palette-system/az-macro/docs/az66jp/rgbled/README.md

# RGBLEDの設定方法
<br>

<table>
  <tr>
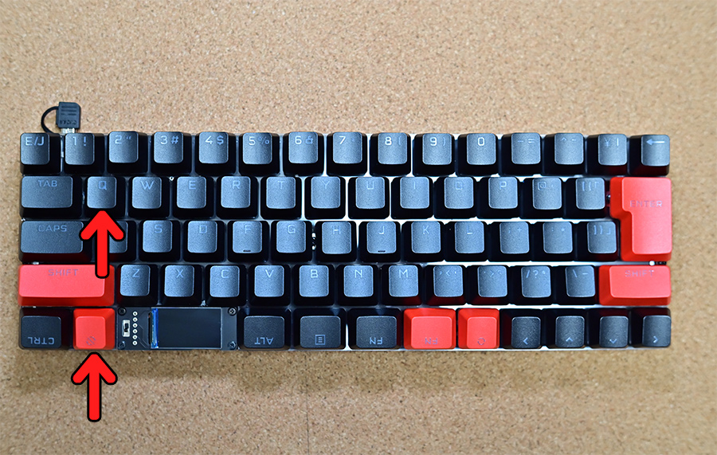
[picture p16: images/az66jp/led_setting_5.jpg]
    <td><br>
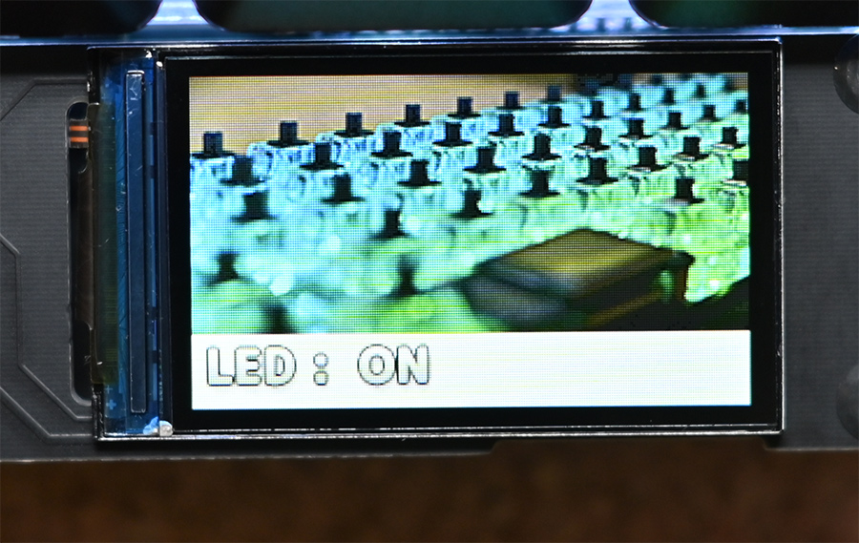
[picture p17: images/az66jp/led_setting_1.jpg]
    </td>
    <td valign="top">
    <b>キー：</b> Fn ＋ Q<br><br>
    <b>ON / OFF</b><br>
    カラーLEDの ON / OFF が切り替えできます。
  </tr>
  <tr>
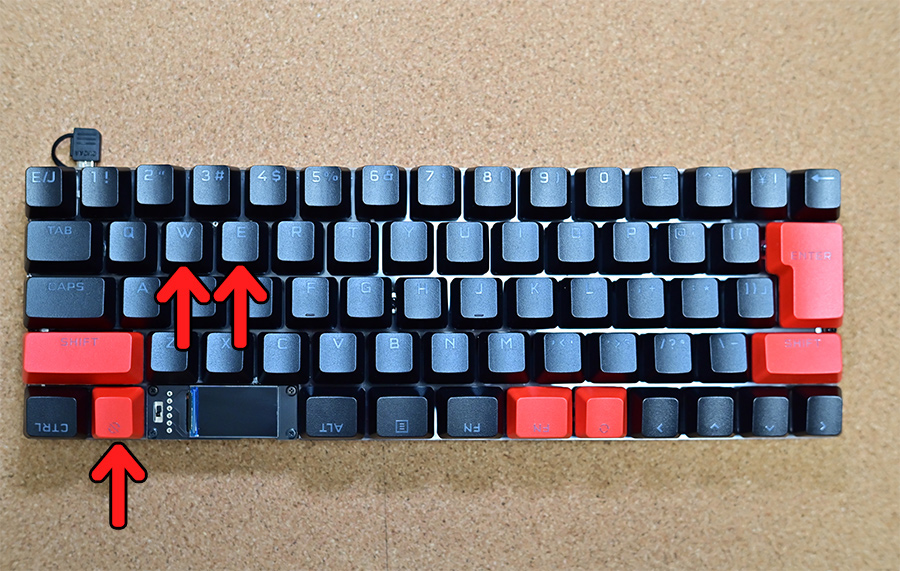
[picture p18: images/az66jp/led_setting_6.jpg]
    <td><br>
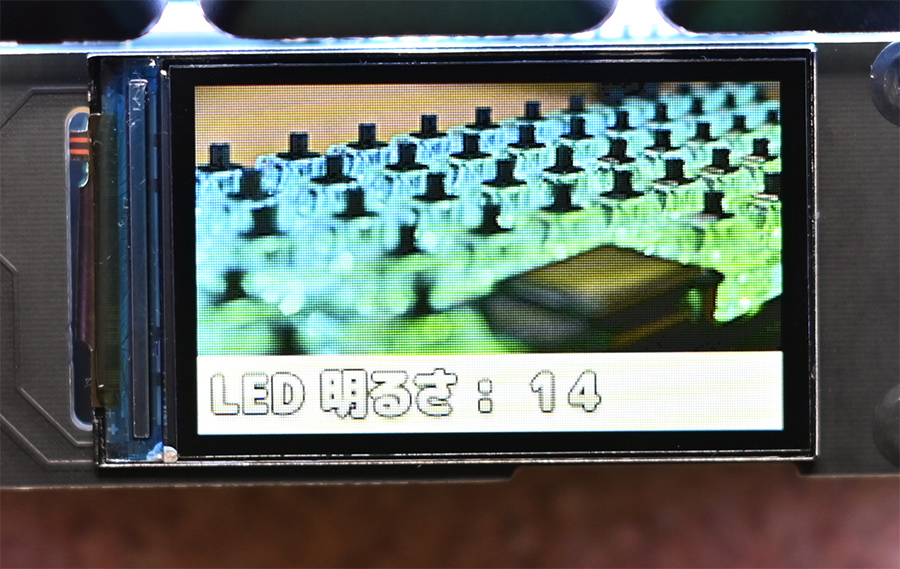
[picture p19: images/az66jp/led_setting_2.jpg]
    </td>
    <td valign="top">
    <b>明るさUP：</b> Fn ＋ W<br><br>
    <b>明るさDOWN：</b> Fn ＋ E<br><br>
    <b>明るさ UP / DOWN</b><br>
    LEDの明るさを0～16段階で設定できます。<br>
  </tr>
  <tr>
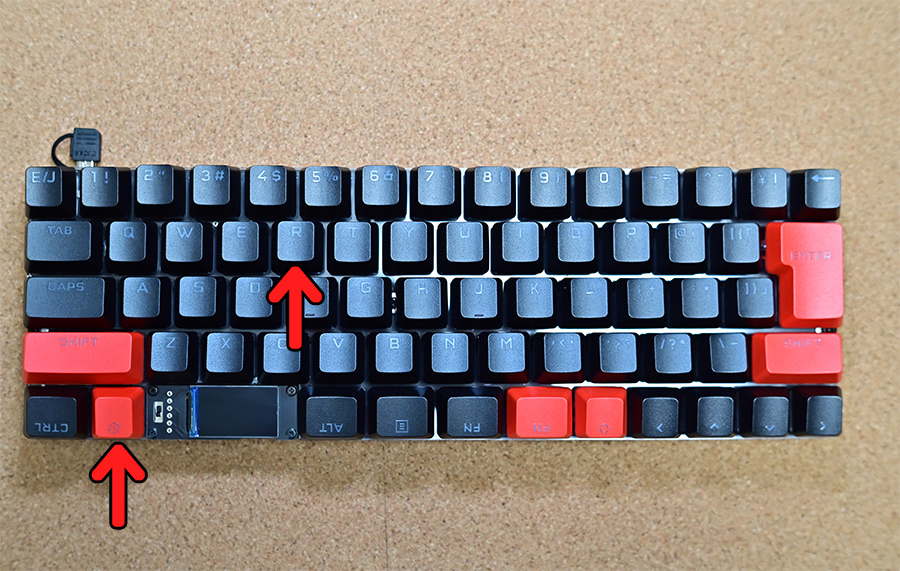
[picture p20: images/az66jp/led_setting_8.jpg]
    <td><br>
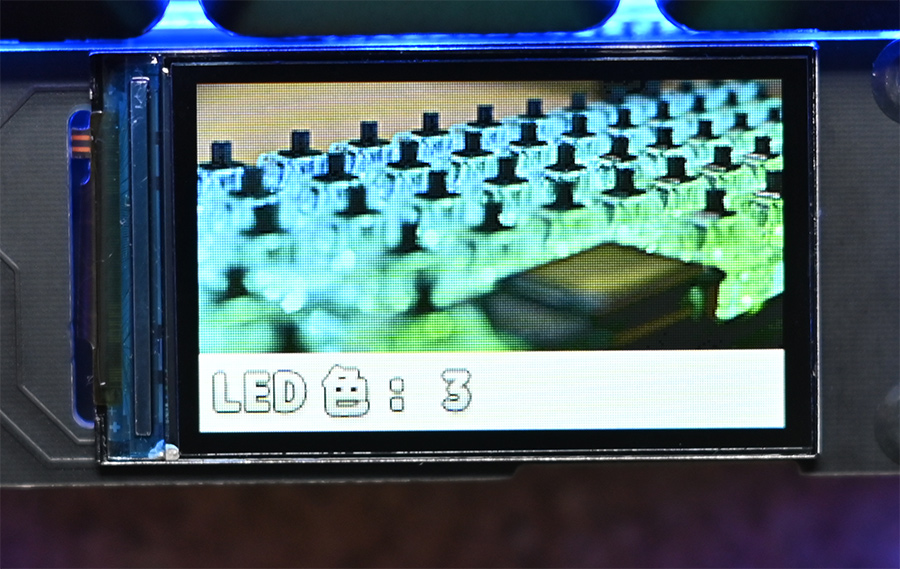
[picture p21: images/az66jp/led_setting_3.jpg]
    </td>
    <td valign="top">
    <b>キー：</b> Fn ＋ R<br><br>
    <b>色変更</b><br>
    光らせるLEDの色を0～5段階で変更できます。<br><br>
    　<b>0 : </b> 白<br>
    　<b>1 : </b> 赤<br>
    　<b>2 : </b> 緑<br>
    　<b>3 : </b> 青<br>
    　<b>4 : </b> 黄<br>
    　<b>5 : </b> 水色<br>
    </td>
  </tr>
  <tr>
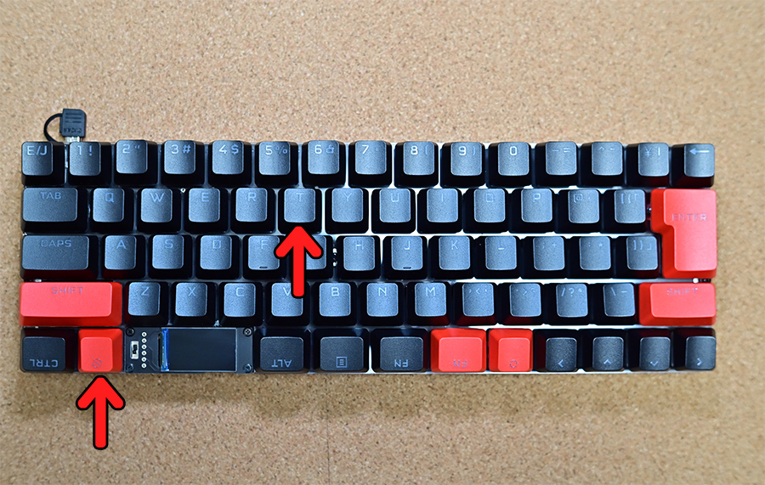
[picture p22: images/az66jp/led_setting_9.jpg]
    <td><br>
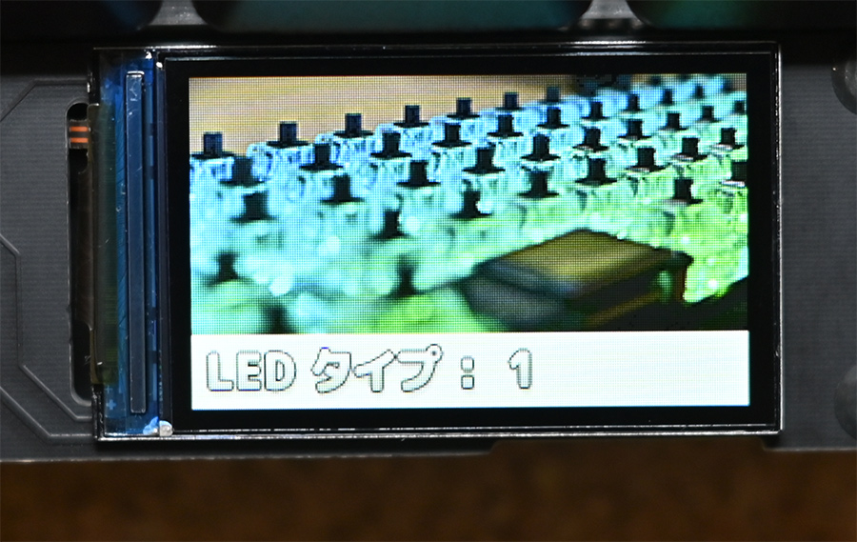
[picture p23: images/az66jp/led_setting_4.jpg]
    </td>
    <td valign="top">
    <b>キー：</b> Fn ＋ T<br><br>
    <b>光らせ方変更</b><br>
    光り方を0～3の4タイプ変更できます。<br><br>
    　<b>0 : </b> 常に点灯<br>
    　<b>1 : </b> 打鍵キーだけ点灯<br>
    　<b>2 : </b> 打鍵キーから周りに広がっていく<br>
    　<b>3 : </b> 常に全てのキーをグラデーション点灯<br>
    </td>
  </tr>
</table>

<br>
<br>
