palette-system/az-macro/docs/az66jp/keydata/README.md

# キー情報

## キーID

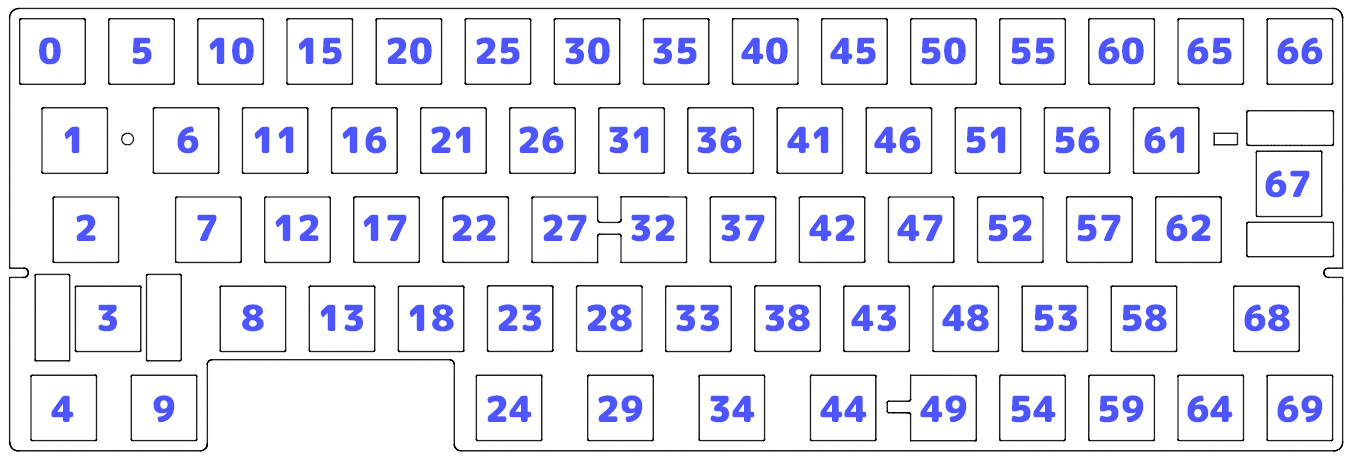
[picture p29: images/az66jp/az66jp_key_id.jpg]


<br>

## LED ID

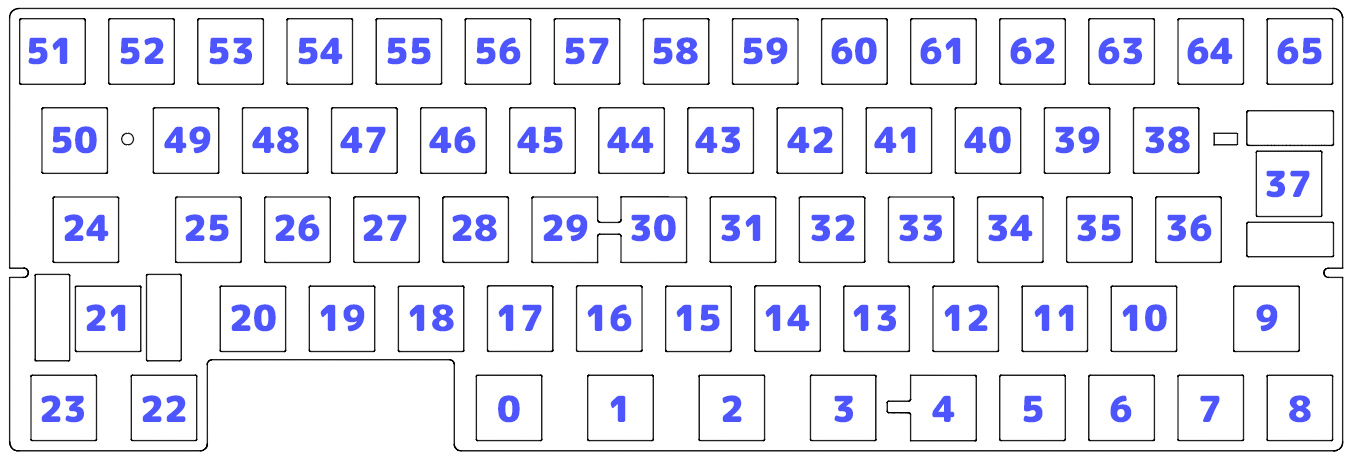
[picture p30: images/az66jp/az66jp_led_num.jpg]
