palette-system/az-macro/docs/setting/key/led/README.md

# キー設定 ＞ LED設定ボタン

<table>
  <tr>
  <td valign="top">
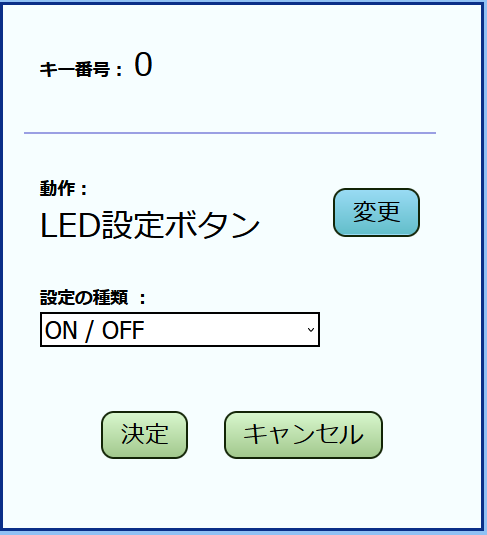
[picture p31: images/key_setting_led.png]
    
    </td>
  <td valign="top">
    <b>設定の種類：ON / OFF</b><br>LEDを光らせるかどうかを変更できます。<br><br>
    <b>設定の種類：明るさUP</b><br>LEDの光の強さを強くします。(0 - 16)<br><br>
    <b>設定の種類：明るさDOWN</b><br>LEDの光の強さを弱くします。(0 - 16)<br><br>
    <b>設定の種類：色変更</b><br>光らせるベースの色を変更できます。(0 - 5)<br><br>
    <b>設定の種類：光らせ方変更</b><br>LEDの光り方を変更できます。(0 -4)<br>
    <br>
    <b>決定：</b><br>　変更した内容を反映してトップに戻ります。<br>
    <br>
    <b>キャンセル：</b><br>　変更した内容を反映せずに設定トップに戻ります。<br>
  </td>
  </tr>
</table>
