palette-system/az-macro/docs/az66jp/heatmap/README.md

# 打鍵ヒートマップ機能の使い方
<br>

<table>
  <tr>
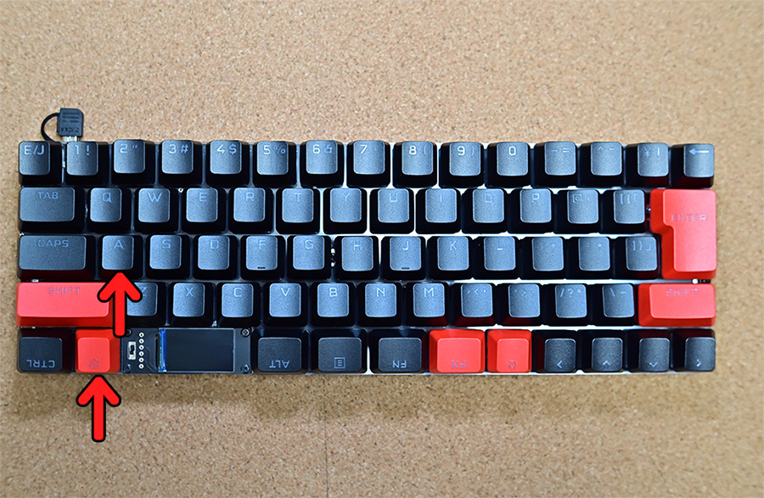
[picture p58: images/az66jp/dakey_1.jpg]
    <td><br>
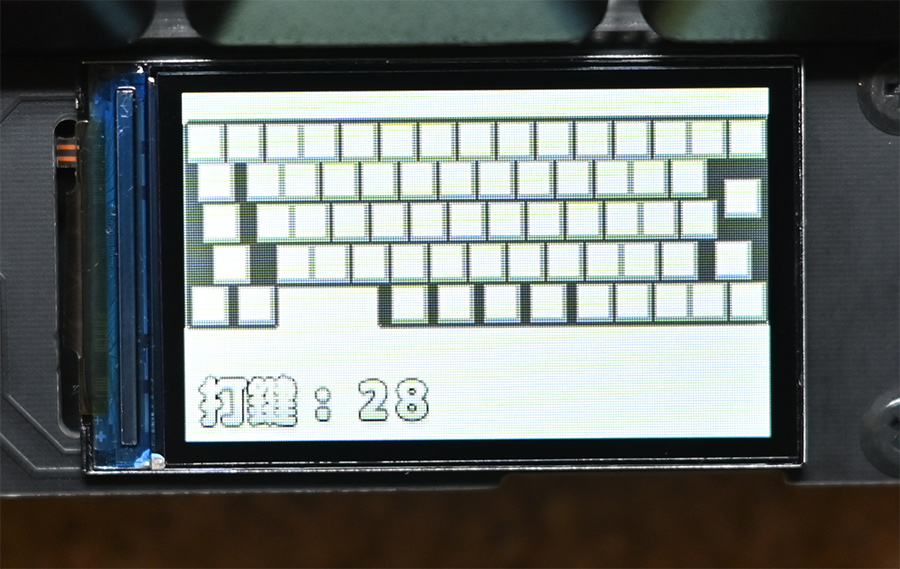
[picture p59: images/az66jp/dakey_6.jpg]
    </td>
    <td valign="top">
    <b>キー：</b> Fn ＋ A<br><br>
    <b>ヒートマップ表示</b><br>
    液晶プレートに打鍵ヒートマップを表示します。<br>
    もう一度押すと元の待ち受け表示に戻ります。</td>
  </tr>
  <tr>
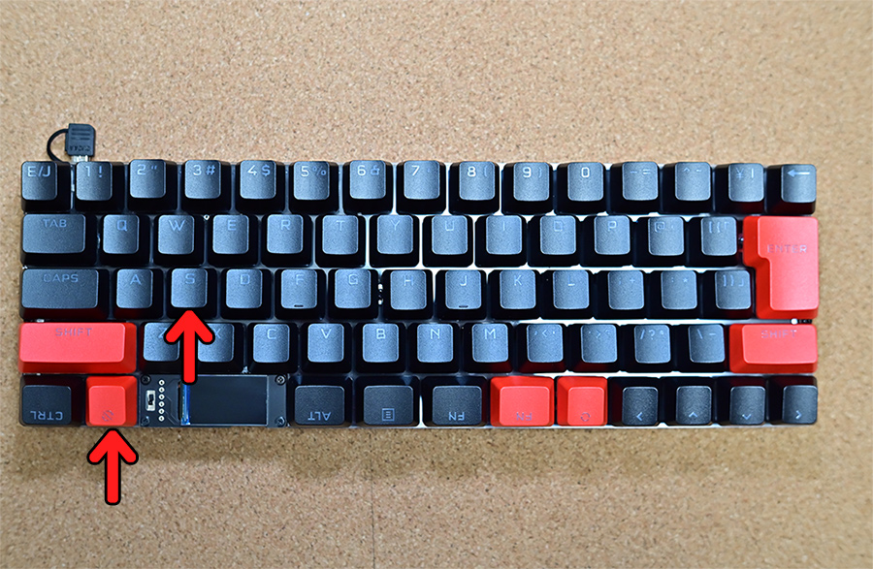
[picture p60: images/az66jp/dakey_2.jpg]
    <td><br>
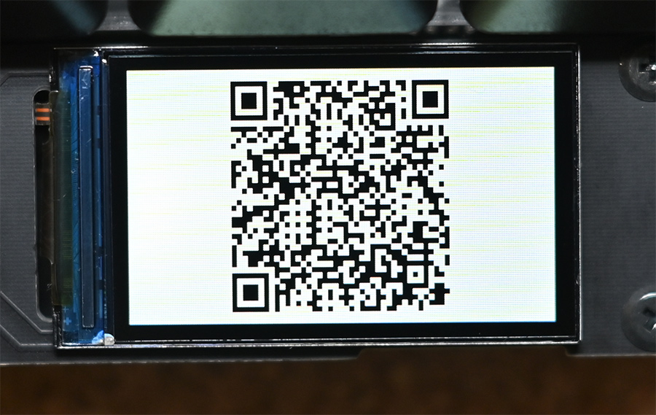
[picture p61: images/az66jp/dakey_5.jpg]
    </td>
    <td valign="top">
    <b>キー：</b> Fn ＋ S<br><br>
    <b>QRコード</b><br>
    現在の打鍵情報をazkey.jpに送信して、スマホやPCから打鍵数を見れるURLのQRコードを表示します。<br>
    何かキーを押すとQRコードの表示が終わります。<br><br>
    ※ 設定ページでWifi接続の設定がしてある必要があります。</td>
  </tr>
  <tr>
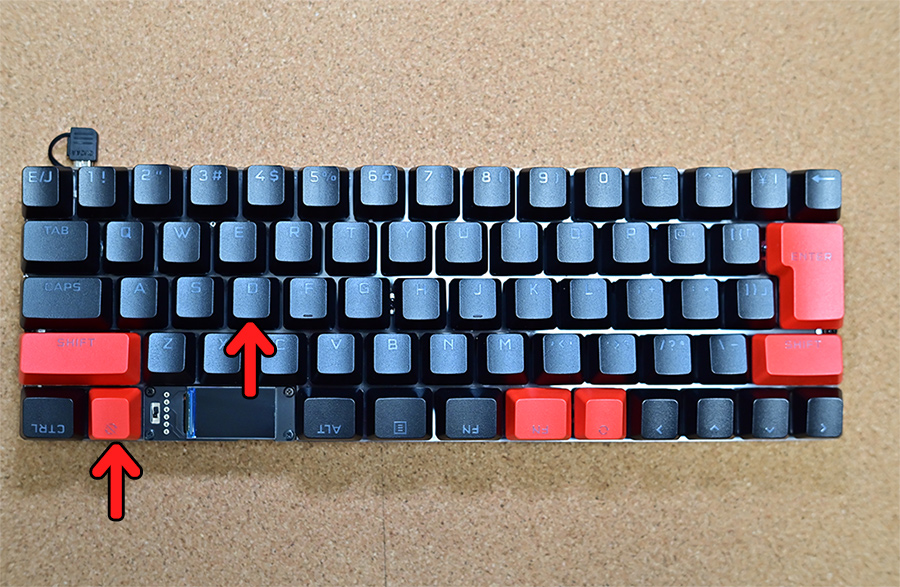
[picture p62: images/az66jp/dakey_3.jpg]
    <td><br>
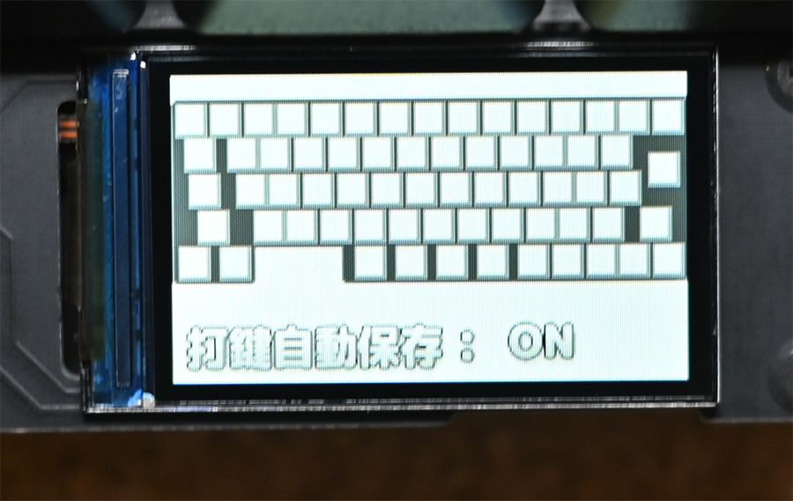
[picture p63: images/az66jp/dakey_7.jpg]
    </td>
    <td valign="top">
    <b>キー：</b> Fn ＋ D<br><br>
    <b>自動保存設定</b><br>
    30分おきに打鍵数を保存するかどうかを変更できます。<br>
    通常は「打鍵数保存」キーを押したタイミングでのみデータを保持していきますが、自動保存設定をONにすると30分おきの情報も保存されます。<br>
    細かくデータが残っていると、QRコードを読み込んでPCやスマホで見た時の時間グラフが細かく表示されます。<br><br>
    ※ 設定ページでWifi接続の設定がしてある必要があります。</td>
  </tr>
  <tr>
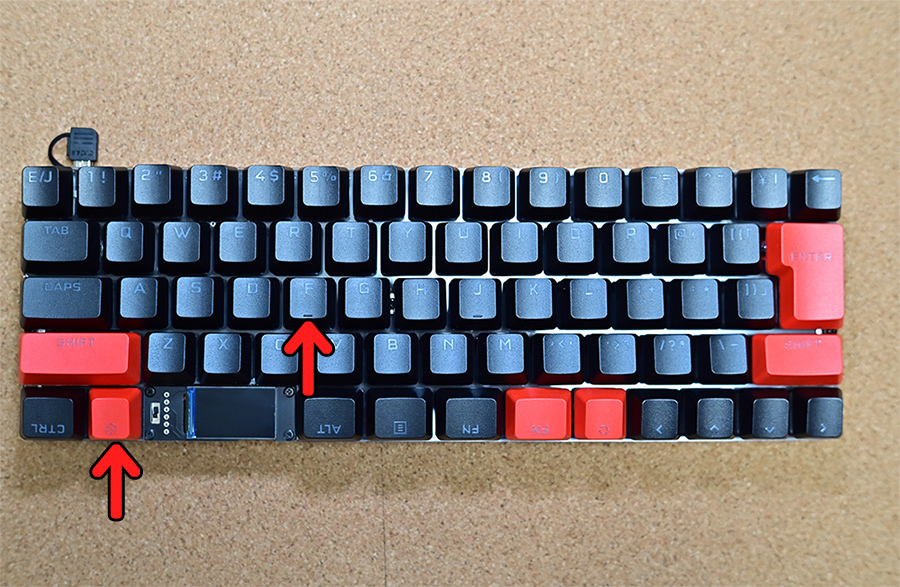
[picture p64: images/az66jp/dakey_4.jpg]
    <td><br>
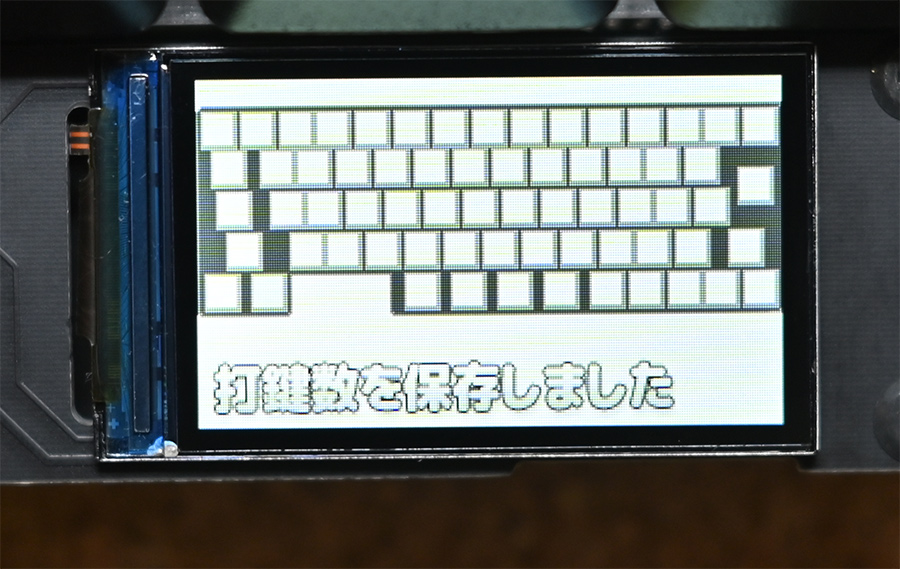
[picture p65: images/az66jp/dakey_8.jpg]
    </td>
    <td valign="top">
    <b>キー：</b> Fn ＋ F<br><br>
    <b>打鍵数保存</b><br>
    現在の打鍵数を保存します。<br>
    細かくデータが残っていると、QRコードを読み込んでPCやスマホで見た時の時間グラフが細かく表示されます。<br><br>
    ※ 設定ページでWifi接続の設定がしてある必要があります。</td>
  </tr>
</table>

<br>
<br>
