palette-system/az-macro/docs/az66jp/ankey/README.md

# 暗記ボタンの使い方
<br>

<table>
  <tr>
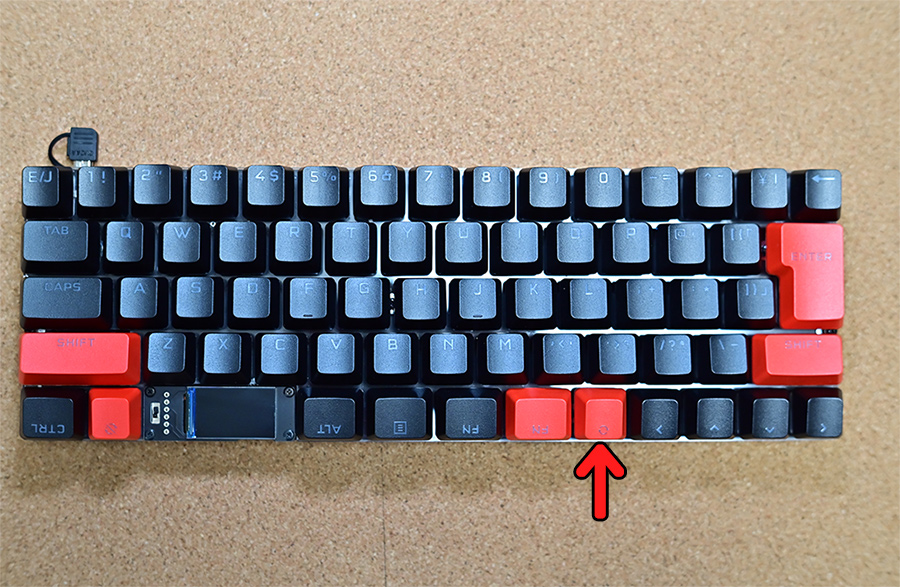
[picture p66: images/az66jp/ankey_1.jpg]
    <td></td>
    <td>暗記ボタンとして登録されているキーを長押しします。</td>
  </tr>
  <tr>
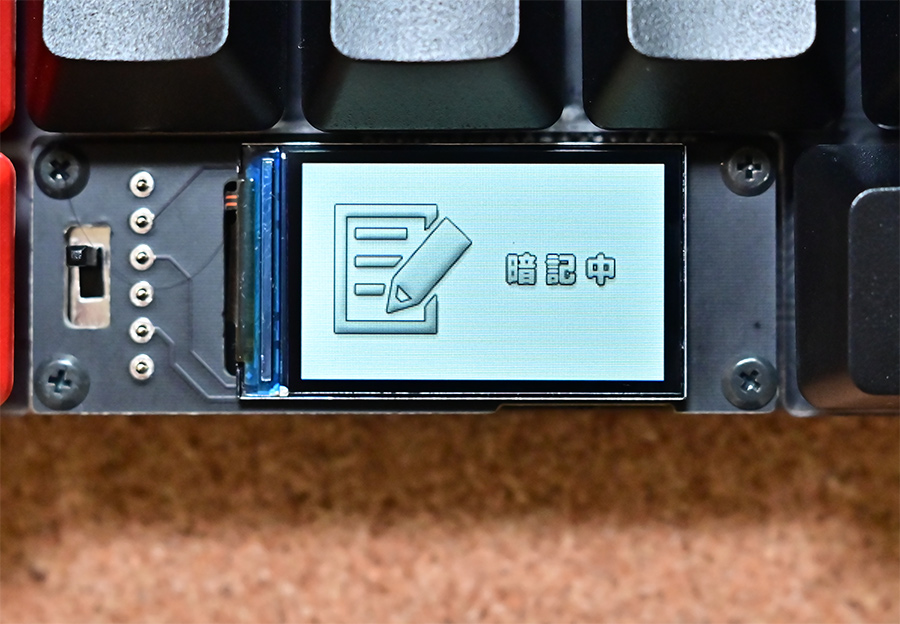
[picture p67: images/az66jp/ankey_2.jpg]
    <td></td>
    <td>液晶プレートに「暗記中」と表示されたら暗記モードに入りましたので、暗記ボタンを離してください。</td>
  </tr>
  <tr>
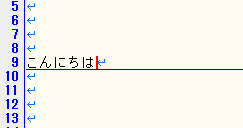
[picture p68: images/az66jp/ankey_3.jpg]
    <td></td>
    <td>暗記モード中にAZ-66JPでキー入力した内容が全て暗記されます。<br><br>
    ※ キーの「押した」「離した」のデータがAZ-66JP内に保存されます。<br>
    ※ １ボタンに対して最大で1000入力まで記憶でき、最大値に達した時点で暗記モードが終了します。<br>
    ※ ここで暗記したデータは電源を落としても残ります。<br><br>
    暗記モードに入る時に長押しした暗記ボタンを短押しすると暗記モード終了になります。
    </td>
  </tr>
  <tr>
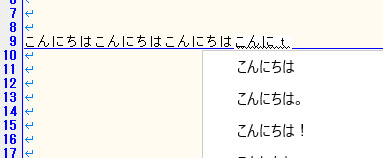
[picture p69: images/az66jp/ankey_4.jpg]
    <td></td>
    <td>暗記データがある状態で暗記ボタンを短押しすると、保存してあるデータが入力されます。<br>
    </td>
  </tr>
</table>

<br>
<br>
