palette-system/az-macro/docs/setting/az66jp/README.md

# AZ-66JP 設定画面の入り方

<table>
  <tr>
  <td valign="top">
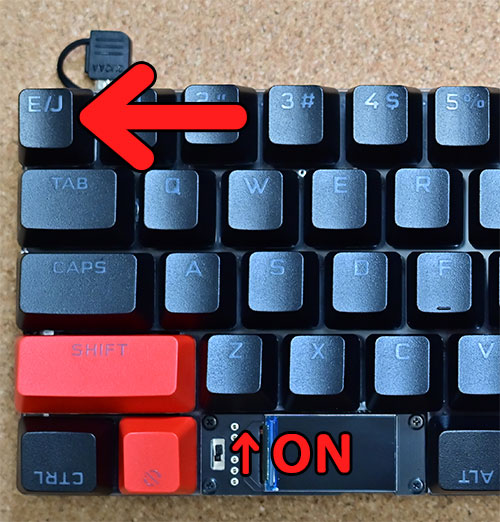
[picture p70: images/az66jp/setting_init.jpg]
    
  </td>
  <td valign="top">
    半角/全角 ボタンを押したままAZ-66JPの電源をONにします。<br>
  </td>
  </tr>
  <tr>
  <td valign="top">
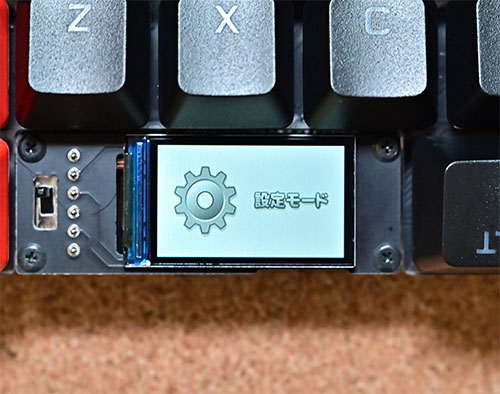
[picture p71: images/az66jp/setting_init_2.jpg]
    
  </td>
  <td valign="top">
    設定モードとして起動すると、液晶プレートに「設定モード」と表示されます。<br><br>
    　※ この画面が出るまで半角/全角ボタンは押したままにして下さい。
  </td>
  </tr>
  <tr>
  <td valign="top">
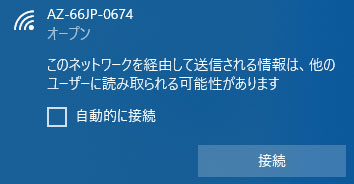
[picture p72: images/az66jp/wifi_ap_setting.jpg]
    
  </td>
  <td valign="top">
    設定モードとして起動した状態で、PCやスマホからWifiアクセスポイントを探すと「AZ-66JP-****」というアクセスポイントがあるので接続します。<br>
  </td>
  </tr>
  <tr>
  <td valign="top">
    
  </td>
  <td valign="top">
    接続完了すると自動的にブラウザが立ち上がり設定画面が開かれます。<br><br>
    　※ 自動的に開かれない場合はブラウザを開き http://192.168.4.1/ にアクセスして下さい。
  </td>
  </tr>
</table>
