palette-system/az-macro/docs/az66jp/photos/README.md

# 商品写真 AZ-66JP

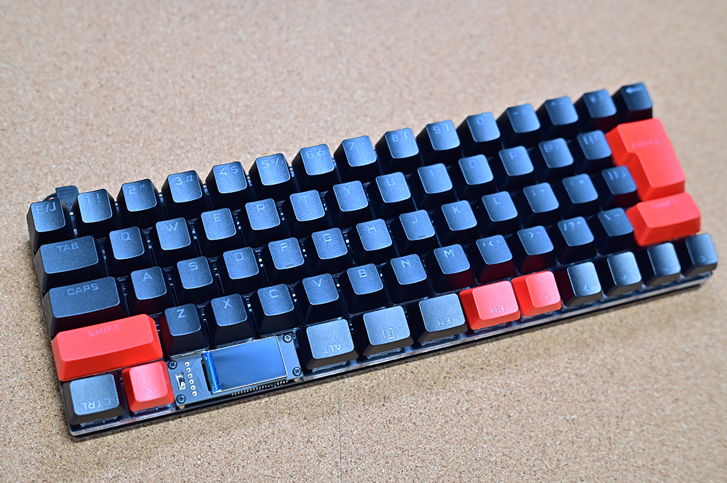
[picture p78: images/az66jp/photo_01.jpg]


<br>

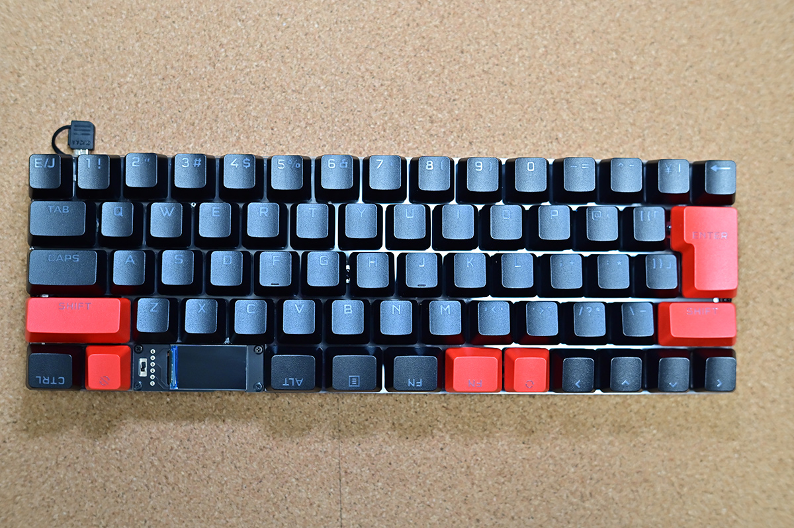
[picture p79: images/az66jp/photo_02.jpg]


<br>

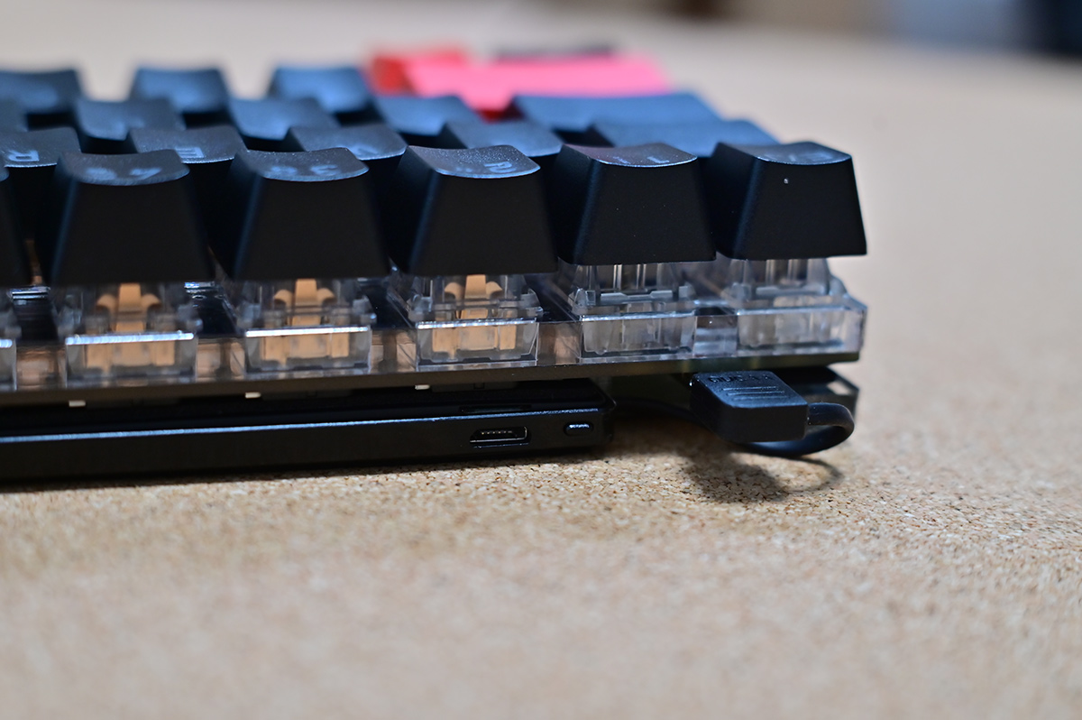
[picture p80: images/az66jp/photo_03.jpg]


<br>

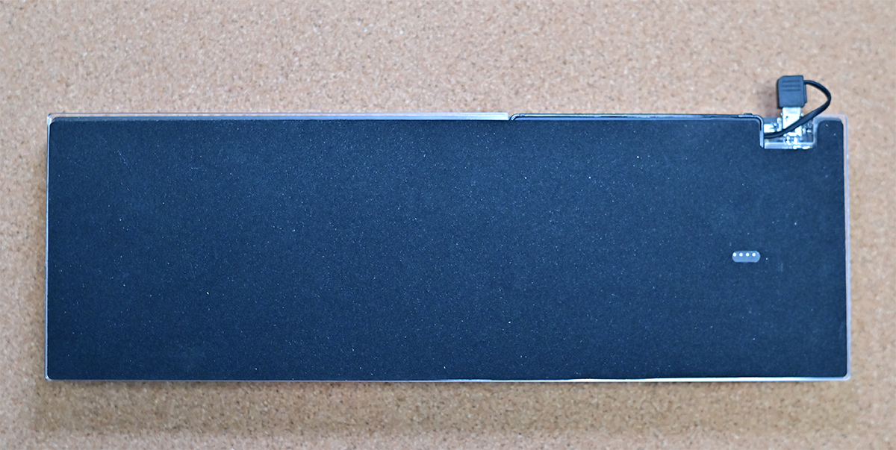
[picture p81: images/az66jp/photo_04.jpg]


<br>

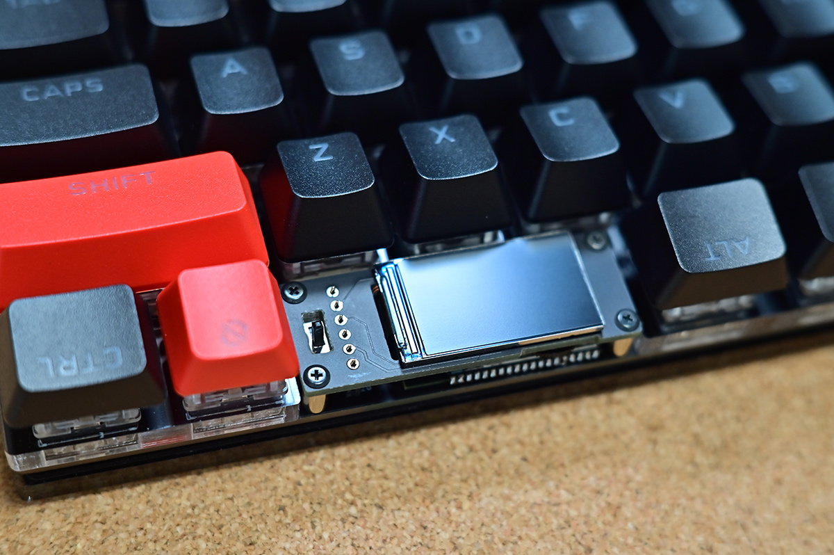
[picture p82: images/az66jp/photo_05.jpg]


<br>

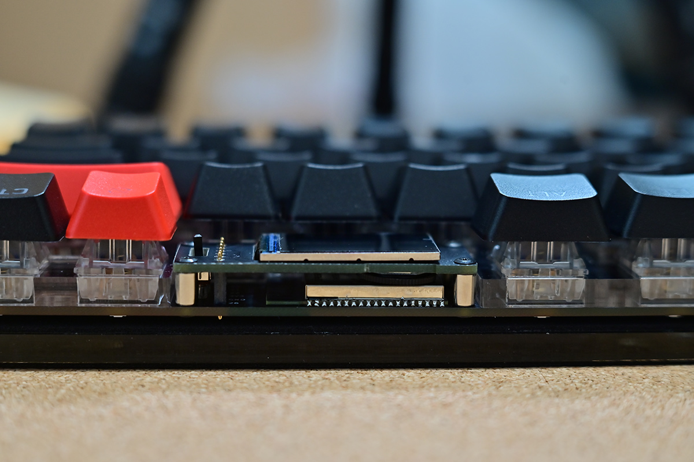
[picture p83: images/az66jp/photo_06.jpg]


<br>

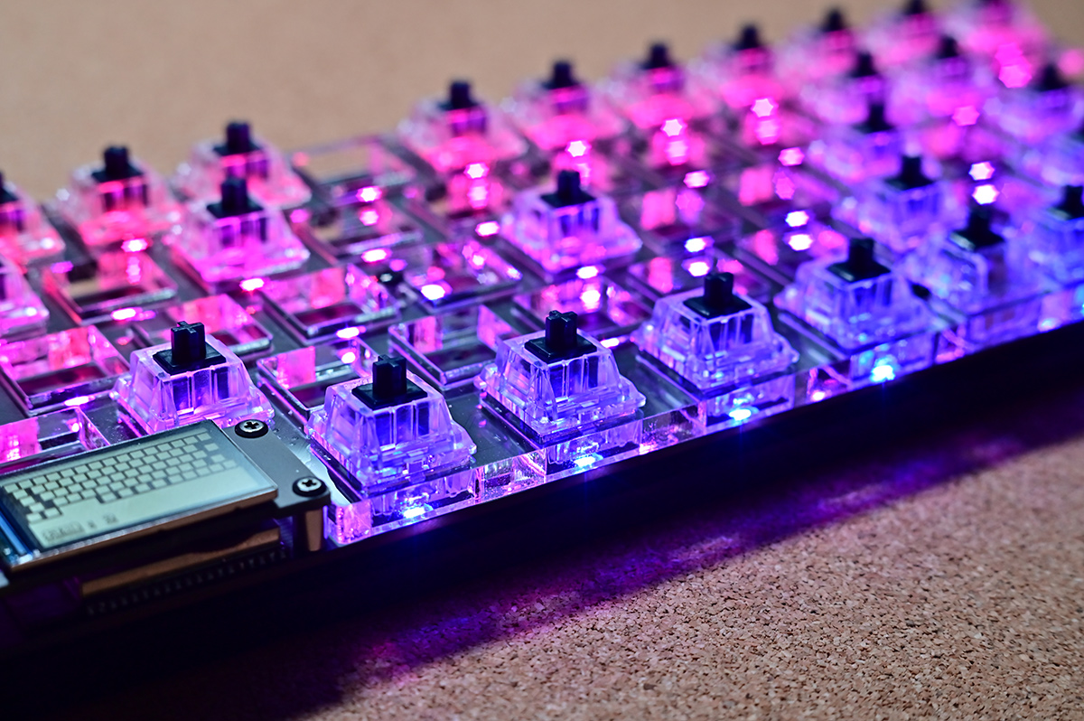
[picture p84: images/az66jp/photo_07.jpg]


<br>

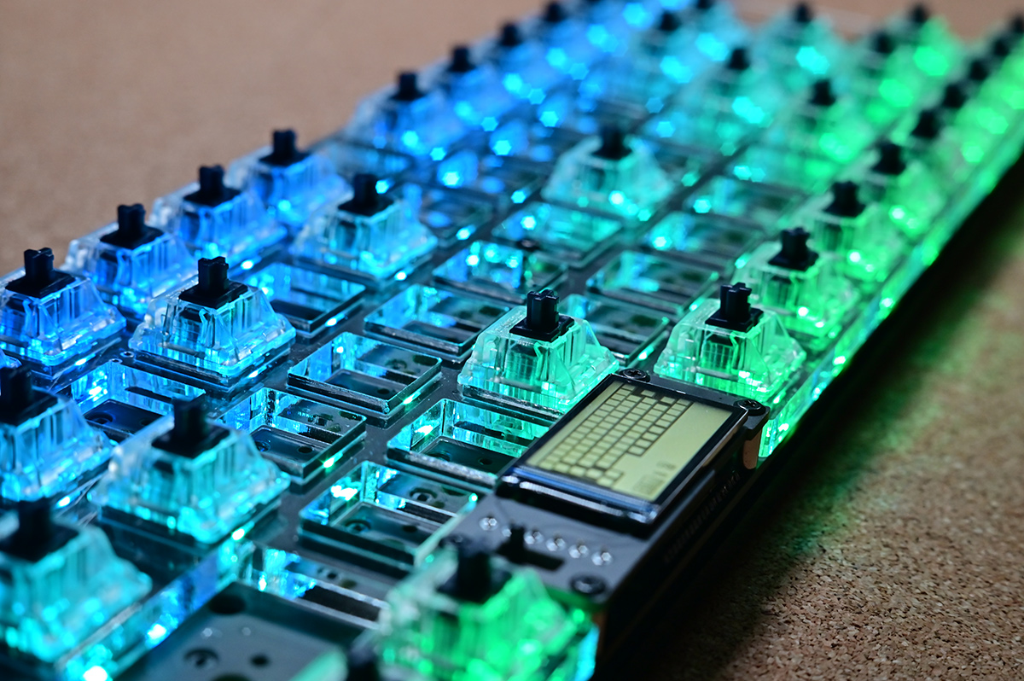
[picture p85: images/az66jp/photo_08.jpg]


<br>

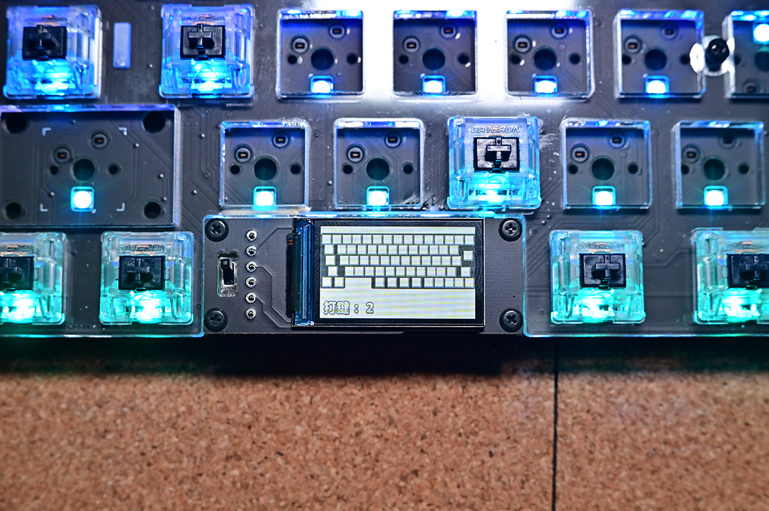
[picture p86: images/az66jp/photo_09.jpg]


<br>

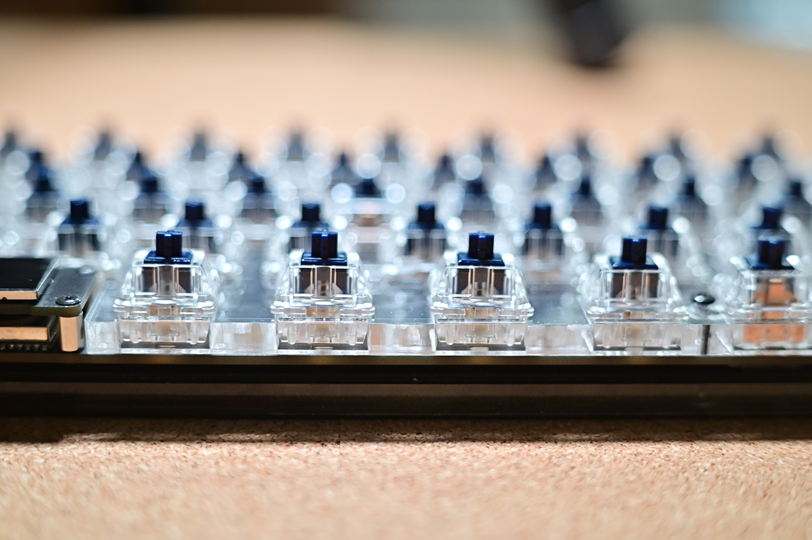
[picture p87: images/az66jp/photo_10.jpg]


<br>

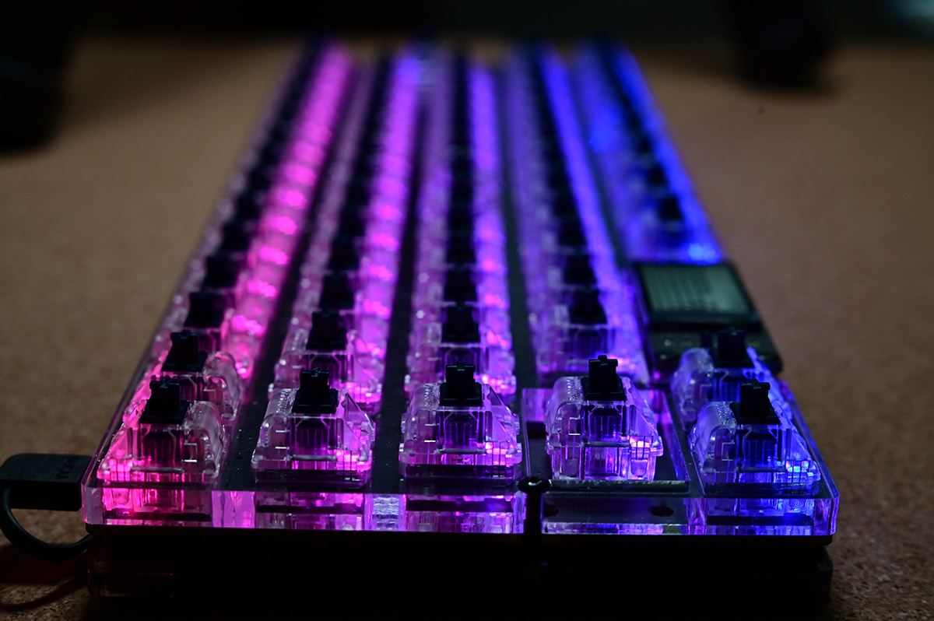
[picture p88: images/az66jp/photo_11.jpg]


<br>

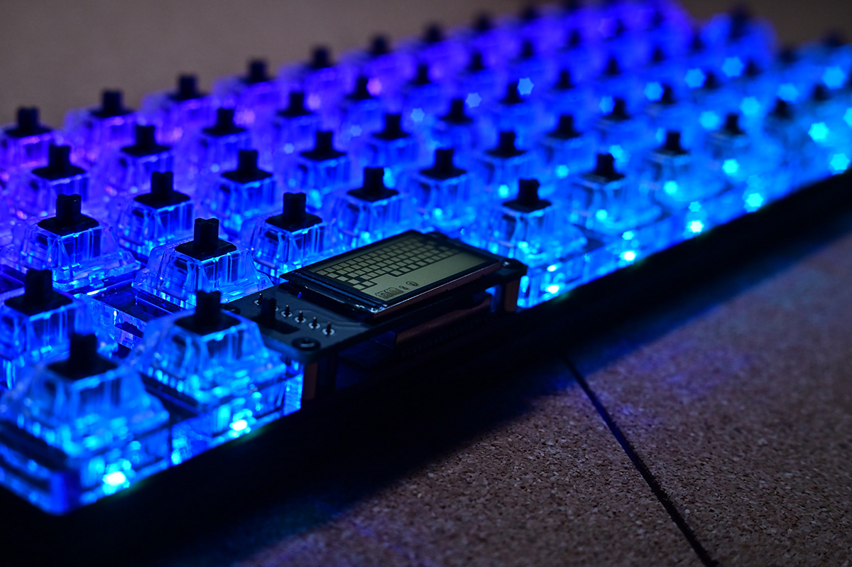
[picture p89: images/az66jp/photo_12.jpg]


<br>

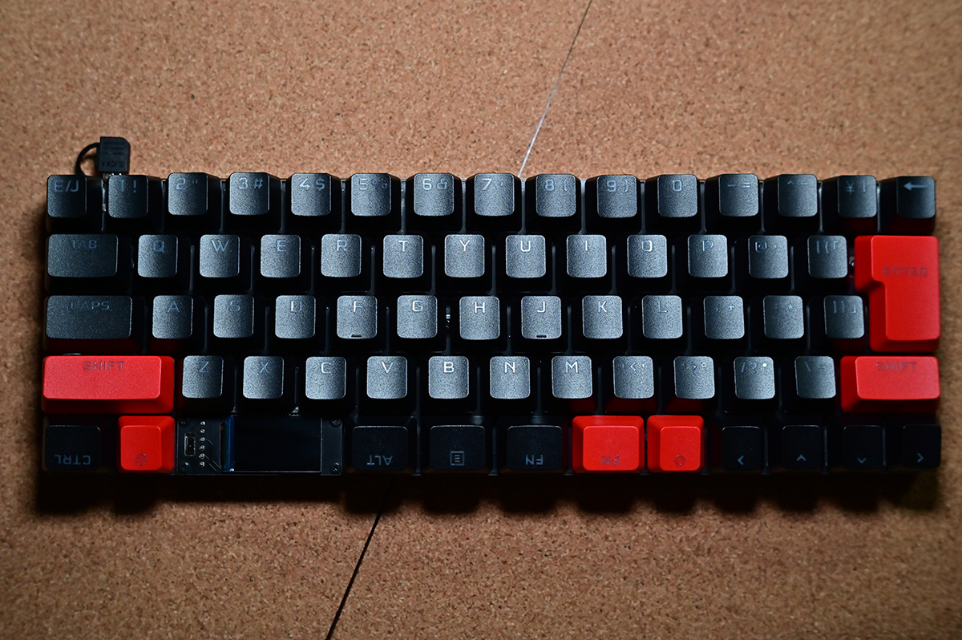
[picture p90: images/az66jp/photo_13.jpg]


<br>

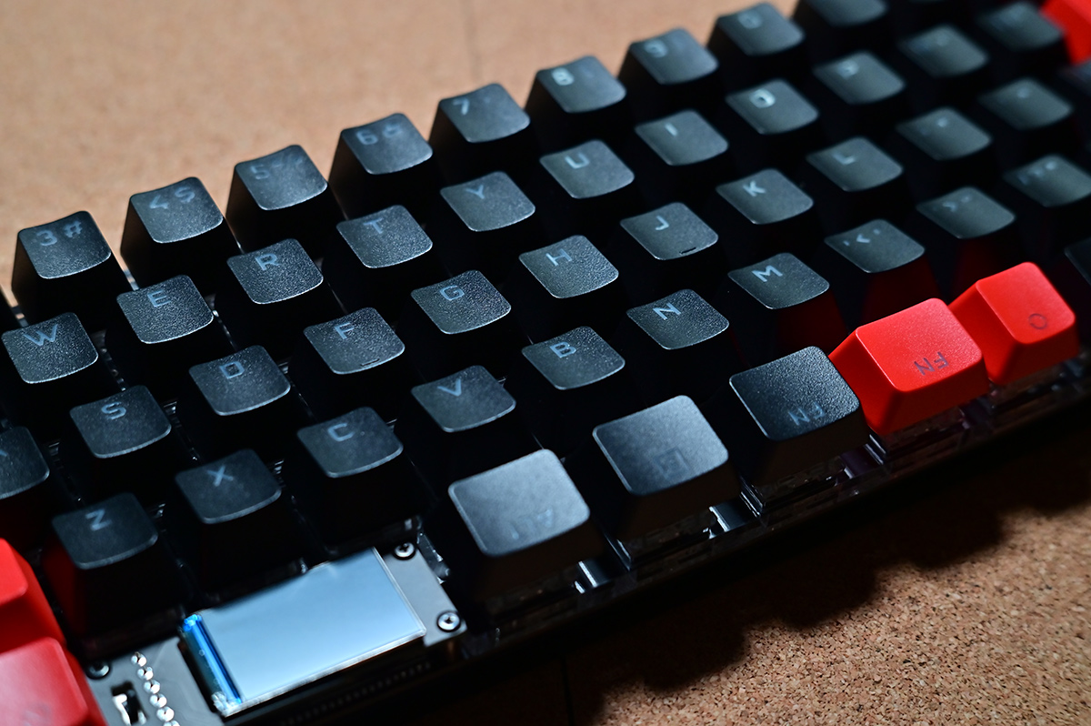
[picture p91: images/az66jp/photo_14.jpg]


<br>

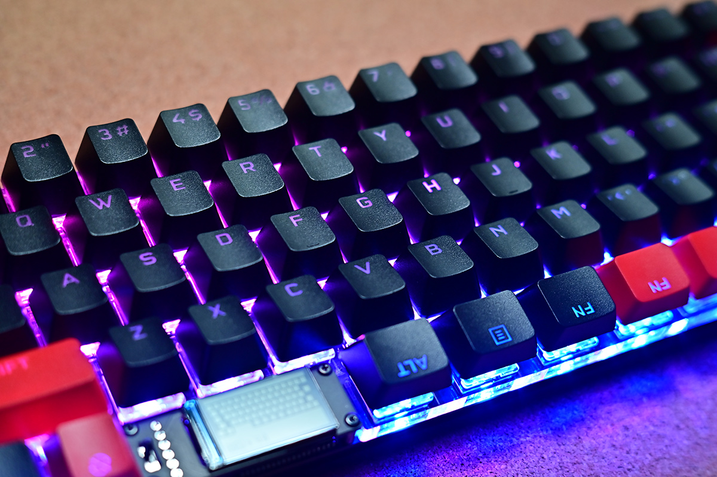
[picture p92: images/az66jp/photo_15.jpg]


<br>

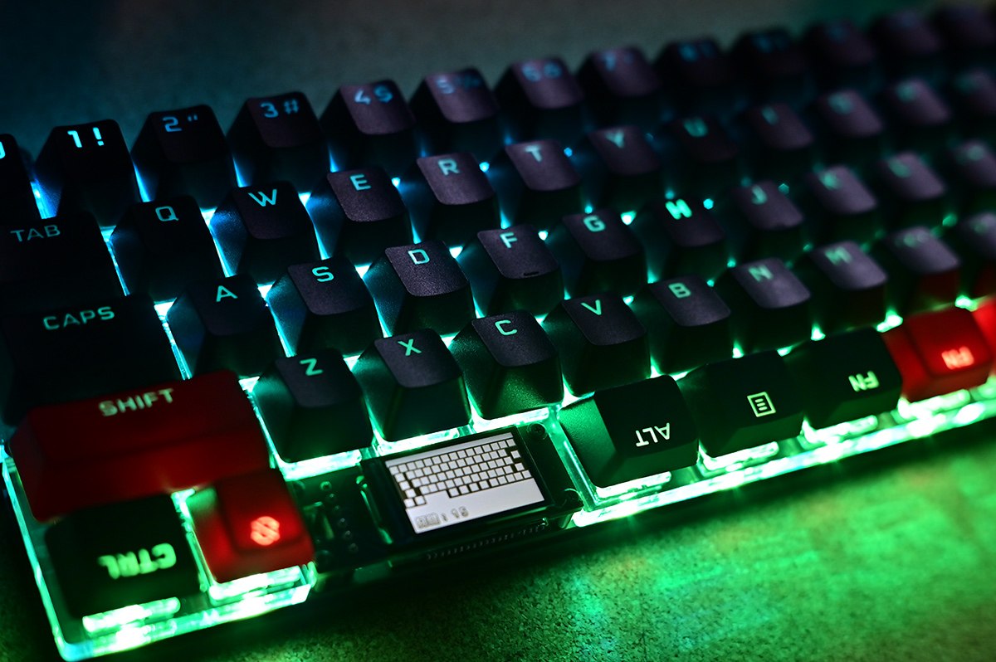
[picture p93: images/az66jp/photo_16.jpg]


<br>

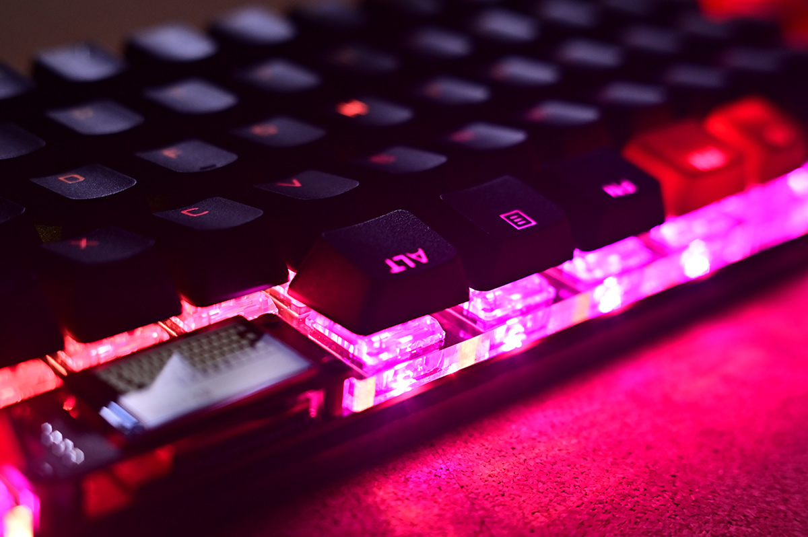
[picture p94: images/az66jp/photo_17.jpg]
