palette-system/az-macro/docs/setting/key/daken/README.md

# キー設定 ＞ 打鍵設定ボタン

<table>
  <tr>
  <td valign="top">
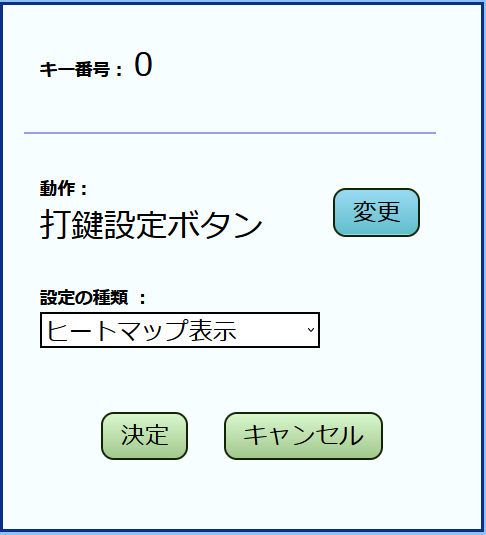
[picture p95: images/key_setting_dakagi.png]
    
    </td>
  <td valign="top">
    <b>設定の種類：ヒートマップ表示</b><br>　本体液晶にヒートマップを表示するかどうかを変更できます<br><br>
    <b>設定の種類：QRコード</b><br>　現在の打鍵情報をazkey.jpに送信して、スマホやPCから打鍵数を見れるURLのQRコードを表示します。<br><br>
    <b>設定の種類：自動保存設定</b><br>　30分おきに打鍵数を保存するかどうかを変更できます。<br><br>
    <b>設定の種類：打鍵数保存</b><br>　現在の打鍵数を本体に保存します。<br><br>
    <br>
    ※ 打鍵数の保存はazkey.jpから現在時刻を取得して、その時刻のデータとして本体に打鍵数を保存します。なのでWiFiに繋がっていないと保存できません。<br><br>
    ※ QRコードを表示した時にazkey.jpに送られるデータは1時間後に削除されます。<br>
    <br>
    <b>決定：</b><br>　変更した内容を反映してトップに戻ります。<br>
    <br>
    <b>キャンセル：</b><br>　変更した内容を反映せずに設定トップに戻ります。<br>
  </td>
  </tr>
</table>
