palette-system/az-macro/docs/setting/key/ankey/README.md

# キー設定 ＞ 暗記ボタン

<table>
  <tr>
  <td valign="top">
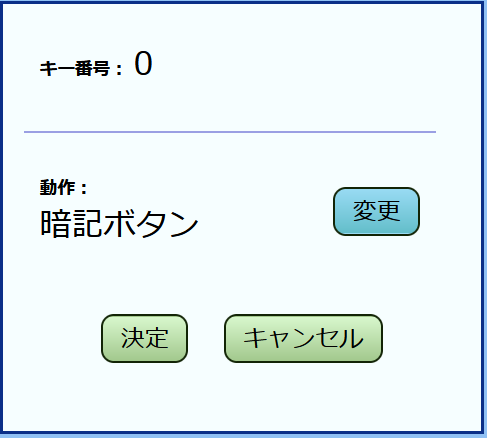
[picture p96: images/key_setting_ankey.png]
    
    </td>
  <td valign="top">
    <b>決定：</b><br>　変更した内容を反映してトップに戻ります。<br>
    <br>
    <b>キャンセル：</b><br>　変更した内容を反映せずに設定トップに戻ります。<br>
  </td>
  </tr>
</table>
