palette-system/az-macro/docs/setting/unit/tft/README.md

# ユニット設定 ＞ 液晶

<table>
  <tr>
  <td valign="top">
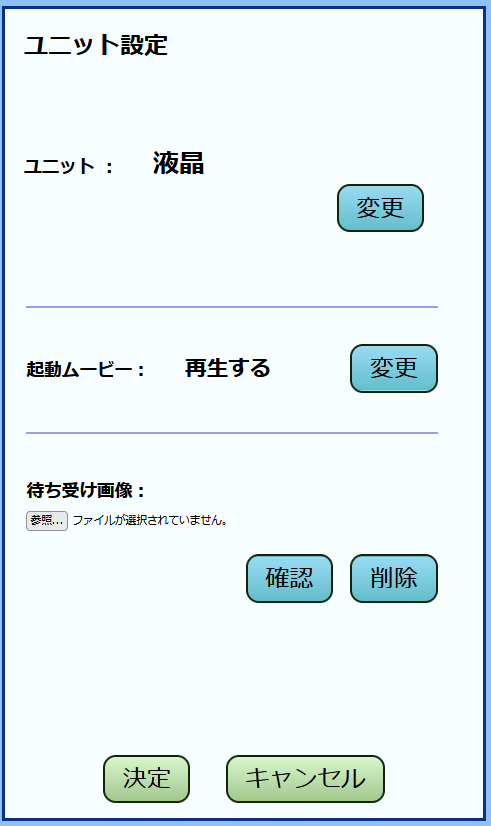
[picture p97: images/unit_setting_tft.png]
    
    </td>
  <td valign="top">
    <b>起動ムービー：</b><br>　起動時のロゴ表示をするかどうか<br>
    <br>
    <b>待ち受け画像：</b><br>　通常時の待ち受けに自分の好きな画像(PNG/JPEG)を指定できます。<br>　<b>「確認」</b>を押すと実際に本体の液晶に画像が表示されます。<br>　<b>「削除」</b>で選択した画像を削除できます。<br>
    <br>
    <b>決定：</b><br>　変更した内容を反映して設定メニューに戻ります。<br>
    <br>
    <b>キャンセル：</b><br>　変更した内容を反映せずに設定メニューに戻ります。<br>
  </td>
  </tr>
</table>
