palette-system/az-macro/docs/webhook/sample/counter/README.md

# 押すたびに増えるカウンタ
パレットシステムで公開しているAPIです。  
リクエストを送信するたびにAPI内部で持っているカウンタをカウントアップしていきます。  
カウントの数字をレスポンスで返してくれるので、キー動作を「HTTPレスポンスを入力」にするとキーを押すたび違う数値がキー入力されます。

## URL
```
https://palette-system.com/ct/
```

## レスポンス内容
内部のカウンタ数値

## 設定例
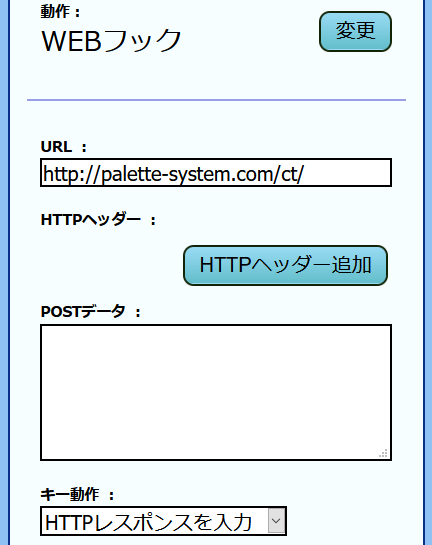
[picture p98: images/web_sample_counter.png]
WEBHookサンプルカウンタ設定例
