palette-system/az-macro/images/az66jp/DSC_7842.jpg

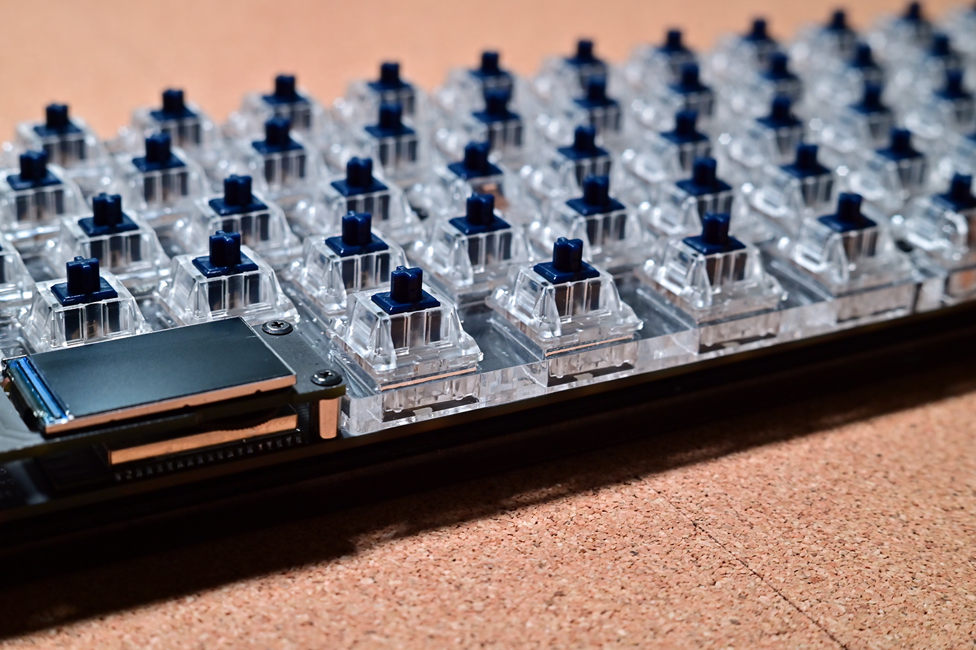
images/az66jp/DSC_7842.jpg
