palette-system/az-macro/images/az66jp/DSC_7892.jpg

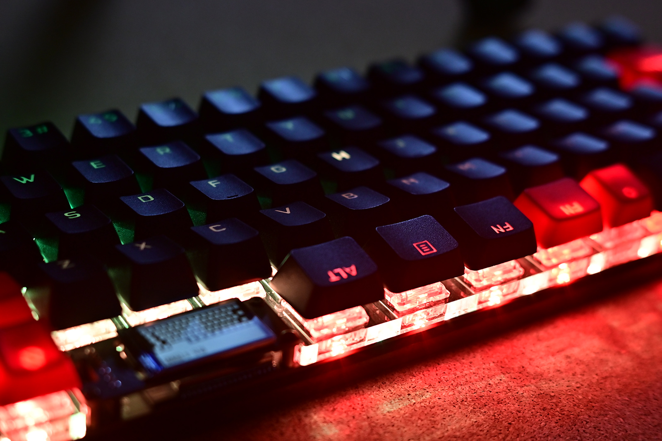
images/az66jp/DSC_7892.jpg
