palette-system/az-macro/images/az66jp/plate_14.jpg

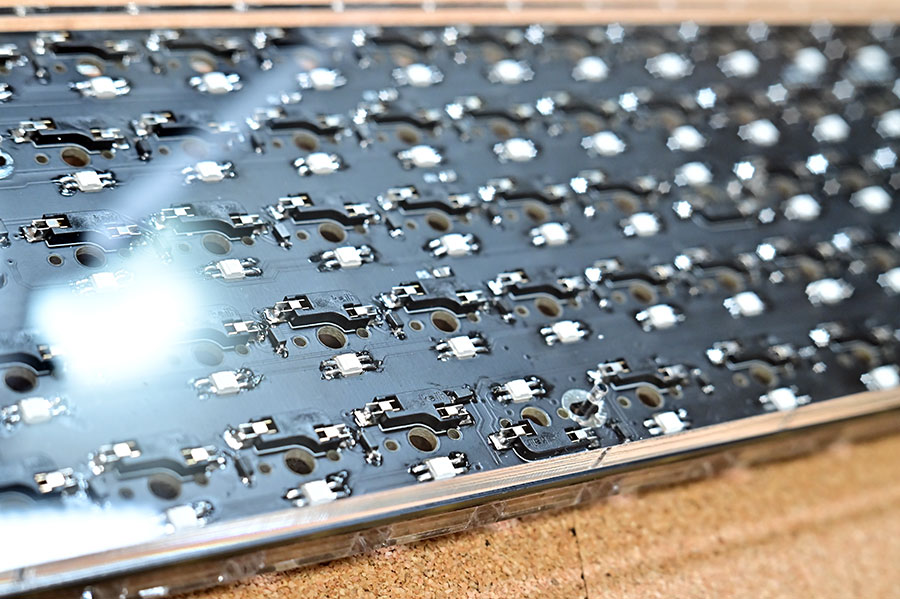
images/az66jp/plate_14.jpg
