palette-system/az-macro/images/spiffs_16mb.png

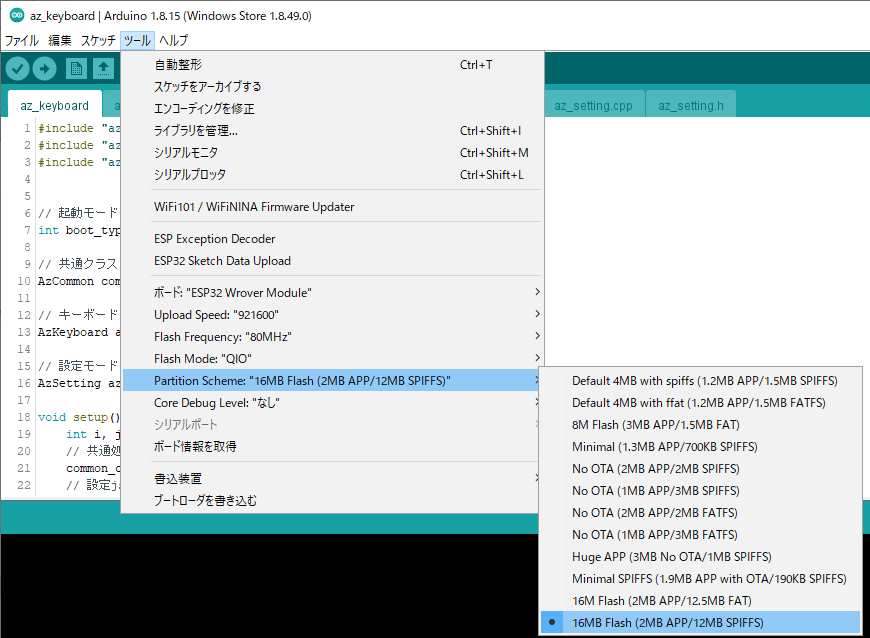
images/spiffs_16mb.png
