palette-system/az-macro/firmware/az_keyboard/az_common.cpp

#include "az_common.h"


// remapに送る用のデータ
uint8_t  *setting_remap;
uint16_t  layer_max;
uint16_t  key_max;

// remap用 キー入力テスト中フラグ
uint16_t  remap_input_test;

// キーが押された時の設定
uint16_t setting_length;
setting_key_press *setting_press;
// wifi設定
uint8_t wifi_data_length;
setting_wifi *wifi_data;
// アクセスポイントパスワード
char *ap_pass_char;
// RGBLED
int8_t rgb_pin;
int8_t matrix_row;
int8_t matrix_col;
int8_t *led_num;
int8_t *key_matrix;
uint8_t led_num_length;
uint8_t key_matrix_length;


// hid
uint16_t hid_vid;
uint16_t hid_pid;

// ステータス表示用ピン番号
int status_pin = -1;

// ステータスLED今0-9
int status_led_bit = 0;

// ステータスLED表示モード
int status_led_mode;

// 液晶オブジェクト
Arduino_ST7789 *tft;

// 液晶表示用オブジェクト
Display *disp;

// rgb_led制御用クラス
Neopixel rgb_led_cls = Neopixel();

//timer オブジェクト
hw_timer_t *timer = NULL;

// WIFI接続オブジェクト
WiFiMulti wifiMulti;

// WIFI接続フラグ
int wifi_conn_flag;

// http用のバッファ
char webhook_buf[WEBFOOK_BUF_SIZE];

// 入力キーの数
int key_input_length;

// キーボードタイプの番号
int keyboard_type_int;

// キーボードの言語(日本語=0/ US=1 / 日本語(US記号) = 2)
uint8_t keyboard_language;

// オプションタイプの番号
int option_type_int;

// トラックボールの方向
uint8_t trackball_direction;

// トラックボールのカーソル移動速度
uint8_t trackball_speed;

// 踏みキーの反転フラグ
bool foot_inversion;

// オープニングムービー再生フラグ
bool op_movie_flag;

// デフォルトのレイヤー番号と、今選択しているレイヤー番号と、最後に押されたレイヤーボタン
int default_layer_no;
int select_layer_no;
int last_select_layer_key;


// 押している最中のキーデータ
press_key_data press_key_list[PRESS_KEY_MAX];

// 押している最中のマウス移動
press_mouse_data press_mouse_list[PRESS_MOUSE_MAX];

// マウスのスクロールボタンが押されているか
bool mouse_scroll_flag;

// オールクリア送信フラグ
int press_key_all_clear;

// eepromのデータ
mrom_data_set eep_data;

// 起動回数
uint32_t boot_count;

// 打鍵数を自動保存するかどうか
uint8_t key_count_auto_save;

// 入力用ピン情報
short col_len;
short row_len;
short direct_len;
short touch_len;
short *col_list;
short *row_list;
short *direct_list;
short *touch_list;


// ステータス用LED点滅
void IRAM_ATTR status_led_write() {
    int set_bit;
    status_led_bit++;
    if (status_led_bit >= 20) status_led_bit = 0;
    if (status_led_mode == 0) {
        set_bit = 0; // 消灯

    } else if (status_led_mode == 1) {
        set_bit = 1; // 点灯
      
    } else if (status_led_mode == 2) {
        // 設定モード
        if (status_led_bit < 5 || (status_led_bit >= 10 && status_led_bit < 15)) {
            set_bit = 1;
        } else {
            set_bit = 0;
        }
      
    } else if (status_led_mode == 3) {
        // ファームウェア更新中
        if (status_led_bit % 2) {
            set_bit = 1;
        } else {
            set_bit = 0;
        }

    } else if (status_led_mode == 4) {
        // wifi接続中
        if (status_led_bit == 0 || status_led_bit == 2 || status_led_bit == 10 || status_led_bit == 12) {
            set_bit = 1;
        } else {
            set_bit = 0;
        }
    }
    if (status_pin >= 0) digitalWrite(status_pin, set_bit);
}

// ランダムな文字生成(1文字)
char getRandomCharLower(void) {
    const char CHARS[] = "abcdefghijklmnopqrstuvwxyz";
    int index = random(0, (strlen(CHARS) - 1));
    char c = CHARS[index];
    return c;
}

// ランダムな文字生成(1文字)
char getRandomNumber(void) {
    const char CHARS[] = "0123456789";
    int index = random(0, (strlen(CHARS) - 1));
    char c = CHARS[index];
    return c;
}

// ランダムな文字列生成(文字数指定)
void getRandomCharsLower(int le, char *cbuf) {
    int i;
    for(i=0; i<le; i++){
        cbuf[i]  = getRandomCharLower();
    }
    cbuf[i] = '\0';
}

// ランダムな文字列生成(数字)
void getRandomNumbers(int le, char *cbuf) {
    int i;
    for(i=0; i<le; i++){
        cbuf[i]  = getRandomNumber();
    }
    cbuf[i] = '\0';
}

// コンストラクタ
AzCommon::AzCommon() {
}

// 共通処理の初期化
void AzCommon::common_start() {
    // 乱数初期化
    randomSeed(millis());
    // ファイルシステム初期化
    if(!SPIFFS.begin(true)){
        ESP_LOGD(LOG_TAG, "SPIFFS begin error\n");
        return;
    }
    // WIFI 接続フラグ
    wifi_conn_flag = 0;
    // 押している最中のキーデータ初期化
    int i;
    for (i=0; i<PRESS_KEY_MAX; i++) {
        press_key_list[i].action_type = -1;
        press_key_list[i].key_num = -1;
        press_key_list[i].key_id = -1;
        press_key_list[i].layer_id = -1;
        press_key_list[i].unpress_time = -1;
    }
    // マウスのスクロールボタンが押されているか
    mouse_scroll_flag = false;
    if (AZ_DEBUG_MODE) Serial.begin(115200);
    // remap用 キー入力テスト中フラグ
    remap_input_test = 0;
}


// ステータスLEDチカ用タイマー登録
void AzCommon::set_status_led_timer() {
    timer = timerBegin(0, 80, true); //timer=1us
    timerAttachInterrupt(timer, &status_led_write, true);
    timerAlarmWrite(timer, 100000, true); // 100ms
    timerAlarmEnable(timer);
}

// WIFI 接続
void AzCommon::wifi_connect() {
    // WIFI 接続
    int i;
    if (wifi_data_length <= 0) {
        ESP_LOGD(LOG_TAG, "wifi : not setting\r\n");
        wifi_conn_flag = 0;
        return;
    }
    // 液晶にWiFi接続中画面を表示する
    if (common_cls.on_tft_unit()) disp->view_wifi_conn();
    // WiFiに接続(一番電波が強いAPへ接続)
    for (i=0; i<wifi_data_length; i++) {
        wifiMulti.addAP(wifi_data[i].ssid, wifi_data[i].pass);
        ESP_LOGD(LOG_TAG, "wifi : [%S] [%S]", wifi_data[i].ssid, wifi_data[i].pass);
    }
    ESP_LOGD(LOG_TAG, "wifi : connect start\r\n");
    i = 0;
    wifi_conn_flag = 1;
    // while (WiFi.status() != WL_CONNECTED) {
    while (wifiMulti.run() != WL_CONNECTED) {
        ESP_LOGD(LOG_TAG, "wifi : try %D\r\n", i);
        delay(1000);
        i++;
        if (i > 20) {
            ESP_LOGD(LOG_TAG, "wifi : connect error\r\n");
            wifi_conn_flag = 0;
            break;
        }
    }
    if (wifi_conn_flag) {
        ESP_LOGD(LOG_TAG, "wifi : connect OK!\r\n");
    }
}

// URLからドメイン名だけ抜き出す
void AzCommon::get_domain(char *url, char *domain_name) {
    int i = 0, j = 0, s = 0;
    while (url[i] > 0) {
        if (s == 0 && url[i] == '/') {
            s = 1;
        } else if (s == 1 && url[i] == '/') {
            s = 2;
        } else if (s == 2) {
            if (url[i] == '/' || url[i] == ':') {
                s = 3;
                domain_name[j] = 0x00;
                break;
            } else if (url[i] == '@') {
                j = 0;
                domain_name[j] = 0x00;
            } else {
                domain_name[j] = url[i];
                j++;
            }
        } else {
            s = 0;
        }
        i++;
    }
    domain_name[j] = 0x00;
}

// webリクエストを送信する(シンプルなGETリクエストのみ)
String AzCommon::send_webhook_simple(char *url) {
    int status_code;
    String res;
    // httpリクエスト用オブジェクト
    HTTPClient http;
    http.begin(url);
    // GET
    status_code = http.GET();
    ESP_LOGD(LOG_TAG, "http status: %D\r\n", status_code);
    if (status_code == HTTP_CODE_OK) {
        res = http.getString();
    } else {
        res = "";
    }
    http.end();
    return res;
}


// POSTでファイルの内容を送信する
String AzCommon::send_webhook_post_file(char *url, char *file_path) {
    if (!wifi_conn_flag) return "";
    status_led_mode = 3;
    // httpリクエスト用オブジェクト
    int status_code;
    HTTPClient_my http;
    String res_body;
    http.begin(url);
    http.addHeader("Content-Type", "application/x-www-form-urlencoded");
    status_code = http.sendPostFile(file_path);
    if (status_code == HTTP_CODE_OK) {
        res_body = http.getString();
    } else {
        res_body = "";
    }
    http.end();
    return res_body;
}

// webリクエストを送信する
String AzCommon::send_webhook(char *setting_data) {
    ESP_LOGD(LOG_TAG, "send_webhook start: %S %D\r\n", setting_data, strlen(setting_data));
    int n = strlen(setting_data) + 1;
    char jchar[n];
    memcpy(jchar, setting_data, n);
    DynamicJsonDocument setting_doc(n + 512);
    deserializeJson(setting_doc, jchar);
    JsonObject prm = setting_doc.as<JsonObject>();
    String url = prm["url"].as<String>();
    int m = url.length() + 1;
    char url_char[m];
    url += "\0";
    url.toCharArray(url_char, m);
    if (url.startsWith("http://") || url.startsWith("https://")) {
        return http_request(url_char, prm);        
    } else {
        return String("url error");
    }
}


// HTTPリクエストを送信する
String AzCommon::http_request(char *url, const JsonObject &prm) {
    if (!wifi_conn_flag) return "";
    status_led_mode = 3;
    ESP_LOGD(LOG_TAG, "http : %S\r\n", url);
    char hkey[64];
    int i;
    int header_len = prm["header"].size();
    // httpリクエスト用オブジェクト
    HTTPClient http;
    http.begin(url);
    // ヘッダー送信
    for (i=0; i<header_len; i++) {
        String hk = prm["header"][i]["key"].as<String>();
        String hv = prm["header"][i]["value"].as<String>();
        hk.toCharArray(hkey, 64);
        hv.toCharArray(webhook_buf, WEBFOOK_BUF_SIZE);
        http.addHeader(hkey, webhook_buf);
    }
    // POSTデータがあればPOST
    String pd = prm["post"].as<String>();
    int status_code;
    if (pd.length() > 0) {
        // POST
        pd.toCharArray(webhook_buf, WEBFOOK_BUF_SIZE);
        status_code = http.POST(webhook_buf);
    } else {
        // GET
        status_code = http.GET();
    }
    ESP_LOGD(LOG_TAG, "http status: %D\r\n", status_code);
    int ot = prm["keyoutput"].as<signed int>();
    if (status_code == HTTP_CODE_OK) {
        String res_body = http.getString();
        http.end();
        status_led_mode = 1;
        if (ot == 0) {
            return "";
        } else if (ot == 1) {
            return String(status_code);
        } else if (ot == 2) {
            return res_body;
        }
        return "";
    } else {
        http.end();
        status_led_mode = 1;
        if (ot == 1) {
            return String(status_code);
        }
        String res_buf = "status code:" + String(status_code);
        return res_buf;
    }
}



// 区切り文字で分割する
int AzCommon::split(String data, char delimiter, String *dst){
    int index = 0;
    int arraySize = (sizeof(data)/sizeof((data)[0]));  
    int datalength = data.length();
    for (int i = 0; i < datalength; i++) {
        char tmp = data.charAt(i);
        if ( tmp == delimiter ) {
            index++;
            if ( index > (arraySize - 1)) return -1;
        }
        else dst[index] += tmp;
    }
    return (index + 1);
}

// レイヤー名、キー名から番号を抜き出す
int split_num(char *c) {
    // _の文字まで進める
    while (c[0] != 0x5F && c[0] != 0x00) {
        c++;
    }
    if (c[0] == 0x5F) c++;
    return String(c).toInt();
}


// JSONデータを読み込む
void AzCommon::load_setting_json() {
    // セッティングJSONを保持する領域
    SpiRamJsonDocument setting_doc(SETTING_JSON_BUF_SIZE);
    JsonObject setting_obj;

    // ファイルが無い場合はデフォルトファイル作成
    if (!SPIFFS.exists(SETTING_JSON_PATH)) {
        if (!create_setting_json()) return;
    }
    // ファイルオープン
    File json_file = SPIFFS.open(SETTING_JSON_PATH);
    if(!json_file){
        // ファイルが開けなかった場合はデフォルトファイル作り直して再起動
        ESP_LOGD(LOG_TAG, "json file open error\n");
        create_setting_json();
        delay(1000);
        ESP.restart(); // ESP32再起動
        return;
    }
    // 読み込み＆パース
    DeserializationError err = deserializeJson(setting_doc, json_file);
    if (err) {
        ESP_LOGD(LOG_TAG, "load_setting_json deserializeJson error\n");
        create_setting_json();
        delay(1000);
        ESP.restart(); // ESP32再起動
        return;
    }
    json_file.close();
    // オブジェクトを保持
    setting_obj = setting_doc.as<JsonObject>();

    // キーボードタイプは必須なので項目が無ければ設定ファイル作り直し(設定ファイル壊れた時用)
    if (!setting_obj.containsKey("keyboard_type")) {
        ESP_LOGD(LOG_TAG, "json not keyboard_type error\n");
        create_setting_json();
        delay(1000);
        ESP.restart(); // ESP32再起動
        return;
    }

    // キーボードタイプの番号を取得する
    get_keyboard_type_int(setting_obj["keyboard_type"].as<String>());

    // HID 設定
    String hidstr;
    if (setting_obj.containsKey("vendorId")) {
        hidstr = setting_obj["vendorId"].as<String>();
        hid_vid = (uint16_t) strtol(&hidstr[2], NULL, 16);
    } else {
        hid_vid = BLE_HID_VID;
    }
    if (setting_obj.containsKey("productId")) {
        hidstr = setting_obj["productId"].as<String>();
        hid_pid = (uint16_t) strtol(&hidstr[2], NULL, 16);
    } else {
        hid_pid = BLE_HID_PID;
    }
    // デフォルトのレイヤー番号設定
    default_layer_no = setting_obj["default_layer"].as<signed int>();
    // 今選択してるレイヤーをデフォルトに
    select_layer_no = default_layer_no;
    // オプションタイプの番号を取得
    option_type_int = 0;
    if (setting_obj.containsKey("option_set") && setting_obj["option_set"].containsKey("type")) {
        get_option_type_int(setting_obj);
    }
    // オープニングムービー再生取得
    op_movie_flag = false;
    if (setting_obj["option_set"]["op_movie"].as<signed int>() > 0) op_movie_flag = true;
    // 入力ピン情報取得
    int i, j, m;
    col_len = setting_obj["keyboard_pin"]["col"].size();
    row_len = setting_obj["keyboard_pin"]["row"].size();
    direct_len = setting_obj["keyboard_pin"]["direct"].size();
    touch_len = setting_obj["keyboard_pin"]["touch"].size();
    direct_list = new short[direct_len];
    col_list = new short[col_len];
    for (i=0; i<col_len; i++) {
        col_list[i] = setting_obj["keyboard_pin"]["col"][i].as<signed int>();
    }
    row_list = new short[row_len];
    for (i=0; i<row_len; i++) {
        row_list[i] = setting_obj["keyboard_pin"]["row"][i].as<signed int>();
    }
    for (i=0; i<direct_len; i++) {
        direct_list[i] = setting_obj["keyboard_pin"]["direct"][i].as<signed int>();
    }
    touch_list = new short[touch_len];
    for (i=0; i<touch_len; i++) {
        touch_list[i] = setting_obj["keyboard_pin"]["touch"][i].as<signed int>();
    }
    // key_input_length = 16 * ioxp_len;
    // キーの設定を取得
    // まずは設定の数を取得
    layer_max = 0;
    key_max = REMAP_KEY_MAX;
    this->get_keymap(setting_obj);



    // wifiの設定読み出し
    String ssid, pass;
    wifi_data_length = setting_obj["wifi"].size(); // wifiの設定数
    wifi_data = new setting_wifi[wifi_data_length];
    for (i=0; i<wifi_data_length; i++) {
        ssid = setting_obj["wifi"][i]["ssid"].as<String>();
        pass = setting_obj["wifi"][i]["pass"].as<String>();
        m = ssid.length() + 1;
        wifi_data[i].ssid = new char[m];
        ssid.toCharArray(wifi_data[i].ssid, m);
        m = pass.length() + 1;
        wifi_data[i].pass = new char[m];
        pass.toCharArray(wifi_data[i].pass, m);
    }
    for (i=0; i<wifi_data_length; i++) {
        ESP_LOGD(LOG_TAG, "wifi setting [ %S , %S ]\n", wifi_data[i].ssid, wifi_data[i].pass );
    }

    // アクセスポイントのパスワード
    String ap_pass = setting_obj["ap"]["pass"].as<String>();
    m = ap_pass.length() + 1;
    ap_pass_char = new char[m];
    ap_pass.toCharArray(ap_pass_char, m);

    // ステータス表示用ピン番号取得
    if (setting_obj.containsKey("status_pin")) {
        status_pin = setting_obj["status_pin"].as<signed int>();
    }
    
    // 設定されているデフォルトレイヤー取得
    default_layer_no = setting_obj["default_layer"].as<signed int>();

    // キーボードの言語取得
    keyboard_language = setting_obj["keyboard_language"].as<signed int>();

    // RGBLED設定の取得
    rgb_pin = -1;
    if (setting_obj.containsKey("rgb_pin")) rgb_pin = setting_obj["rgb_pin"].as<signed int>();
    matrix_row = -1;
    if (setting_obj.containsKey("matrix_row")) matrix_row = setting_obj["matrix_row"].as<signed int>();
    matrix_col = -1;
    if (setting_obj.containsKey("matrix_col")) matrix_col = setting_obj["matrix_col"].as<signed int>();

    led_num_length = setting_obj["led_num"].size();
    key_matrix_length = setting_obj["key_matrix"].size();
    if (led_num_length > 0) {
        led_num = new int8_t[led_num_length];
        for (i=0; i<led_num_length; i++) {
            led_num[i] = setting_obj["led_num"][i].as<signed int>();
        }
    }
    if (key_matrix_length > 0) {
        key_matrix = new int8_t[key_matrix_length];
        for (i=0; i<key_matrix_length; i++) {
            key_matrix[i] = setting_obj["key_matrix"][i].as<signed int>();
        }
    }

}

// キーマップ用に確保しているメモリを解放
void AzCommon::clear_keymap() {
    int i;
    setting_normal_input normal_input;
    for (i=0; i<setting_length; i++) {
        if (setting_press[i].action_type == 1) { // 通常キー
            memcpy(&normal_input, setting_press[i].data, sizeof(setting_normal_input));
            delete[] normal_input.key;
            delete setting_press[i].data;
        } else if (setting_press[i].action_type == 2) { // テキスト入力
            delete[] setting_press[i].data;
        } else if (setting_press[i].action_type == 3) { // レイヤー切り替え
            delete setting_press[i].data;
        } else if (setting_press[i].action_type == 4) { // WEBフック
            delete[] setting_press[i].data;
        } else if (setting_press[i].action_type == 5) { // マウス移動
            delete setting_press[i].data;
        } else if (setting_press[i].action_type == 7) { // LED設定ボタン
            delete setting_press[i].data;
        } else if (setting_press[i].action_type == 8) { // 打鍵設定ボタン
            delete setting_press[i].data;
        }
    }
    delete[] setting_press;
}

// JSONデータからキーマップの情報を読み込む
void AzCommon::get_keymap(JsonObject setting_obj) {
    int i, j, k, m, at, s;
    char lkey[16];
    char kkey[16];
    uint16_t lnum, knum;
    JsonObject::iterator it_l;
    JsonObject::iterator it_k;
    JsonObject layers, keys;
    JsonObject press_obj;
    String text_str;
    setting_normal_input normal_input;
    setting_layer_move layer_move_input;
    setting_mouse_move mouse_move_input;
    // まずはキー設定されている数を取得
    layers = setting_obj["layers"].as<JsonObject>();
    setting_length = 0;
    for (it_l=layers.begin(); it_l!=layers.end(); ++it_l) {
        setting_length += setting_obj["layers"][it_l->key().c_str()]["keys"].size();
    }
    ESP_LOGD(LOG_TAG, "setting total %D\n", setting_length);
    // 設定数分メモリ確保
    ESP_LOGD(LOG_TAG, "mmm: %D %D\n", heap_caps_get_free_size(MALLOC_CAP_32BIT), heap_caps_get_free_size(MALLOC_CAP_8BIT) );
    setting_press = new setting_key_press[setting_length];
    ESP_LOGD(LOG_TAG, "mmm: %D %D\n", heap_caps_get_free_size(MALLOC_CAP_32BIT), heap_caps_get_free_size(MALLOC_CAP_8BIT) );
    // キー設定読み込み
    i = 0;
    layer_max = 0;
    for (it_l=layers.begin(); it_l!=layers.end(); ++it_l) {
        sprintf(lkey, "%S", it_l->key().c_str());
        lnum = split_num(lkey);
        layer_max++;
        keys = setting_obj["layers"][lkey]["keys"].as<JsonObject>();
        for (it_k=keys.begin(); it_k!=keys.end(); ++it_k) {
            sprintf(kkey, "%S", it_k->key().c_str());
            knum = split_num(kkey);
            // Serial.printf("get_keymap: %S %S [ %D %D ]\n", lkey, kkey, lnum, knum);
            press_obj = setting_obj["layers"][lkey]["keys"][kkey]["press"].as<JsonObject>();
            setting_press[i].layer = lnum;
            setting_press[i].key_num = knum;
            setting_press[i].action_type = press_obj["action_type"].as<signed int>();
            if (setting_press[i].action_type == 1) {
                // 通常入力
                normal_input.key_length = press_obj["key"].size();
                normal_input.key = new uint16_t[normal_input.key_length];
                for (j=0; j<normal_input.key_length; j++) {
                      normal_input.key[j] = press_obj["key"][j].as<signed int>();
                }
                if (press_obj.containsKey("repeat_interval")) {
                    normal_input.repeat_interval = press_obj["repeat_interval"].as<signed int>();
                } else {
                    normal_input.repeat_interval = 51;
                }
                if (press_obj.containsKey("hold")) {
                    normal_input.hold = press_obj["hold"].as<signed int>();
                } else {
                    normal_input.hold = 0;
                }
                setting_press[i].data = (char *)new setting_normal_input;
                memcpy(setting_press[i].data, &normal_input, sizeof(setting_normal_input));
            } else if (setting_press[i].action_type == 2) {
                // テキスト入力
                text_str = press_obj["text"].as<String>();
                m = text_str.length() + 1;
                setting_press[i].data = new char[m];
                text_str.toCharArray(setting_press[i].data, m);
            } else if (setting_press[i].action_type == 3) {
                // レイヤー切り替え
                layer_move_input.layer_id = press_obj["layer"].as<signed int>();
                layer_move_input.layer_type = press_obj["layer_type"].as<signed int>();
                if (layer_move_input.layer_type == 0) layer_move_input.layer_type = 0x51; // 切り替え方法の指定が無かった場合はMO(押している間切り替わる)
                setting_press[i].data = (char *)new setting_layer_move;
                memcpy(setting_press[i].data, &layer_move_input, sizeof(setting_layer_move));
            } else if (setting_press[i].action_type == 4) {
                // WEBフック
                text_str = "";
                serializeJson(press_obj["webhook"], text_str);
                m = text_str.length() + 1;
                setting_press[i].data = new char[m];
                text_str.toCharArray(setting_press[i].data, m);
                
            } else if (setting_press[i].action_type == 5) {
                // マウス移動
                mouse_move_input.x = press_obj["move"]["x"].as<signed int>();
                mouse_move_input.y = press_obj["move"]["y"].as<signed int>();
                mouse_move_input.speed = press_obj["move"]["speed"].as<signed int>();
                setting_press[i].data = (char *)new setting_mouse_move;
                memcpy(setting_press[i].data, &mouse_move_input, sizeof(setting_mouse_move));

            } else if (setting_press[i].action_type == 6) {
                // 暗記ボタン

            } else if (setting_press[i].action_type == 7) {
                // LED設定ボタン
                setting_press[i].data = new char;
                *setting_press[i].data = press_obj["led_setting_type"].as<signed int>();
                
            } else if (setting_press[i].action_type == 8) {
                // 打鍵設定ボタン
                setting_press[i].data = new char;
                *setting_press[i].data = press_obj["dakagi_settype"].as<signed int>();

            }
            i++;
        }
    }
  
    // ログに出力して確認
    for (i=0; i<setting_length; i++) {
        if (setting_press[i].action_type == 1) {
            memcpy(&normal_input, setting_press[i].data, sizeof(setting_normal_input));
            ESP_LOGD(LOG_TAG, "setting_press %D %D %D %D [%D, %D]", i, setting_press[i].layer, setting_press[i].key_num, setting_press[i].action_type, normal_input.key_length, normal_input.repeat_interval);
            for (j=0; j<normal_input.key_length; j++) {
                ESP_LOGD(LOG_TAG, "setting_press %D ", normal_input.key[j]);
            }
        } else if (setting_press[i].action_type == 2) {
            ESP_LOGD(LOG_TAG, "setting_press %D %D %D %D [ %S ]\n", i, setting_press[i].layer, setting_press[i].key_num, setting_press[i].action_type, setting_press[i].data);
        } else if (setting_press[i].action_type == 3) {
            ESP_LOGD(LOG_TAG, "setting_press %D %D %D %D [ %D ]\n", i, setting_press[i].layer, setting_press[i].key_num, setting_press[i].action_type, *setting_press[i].data);
        } else if (setting_press[i].action_type == 4) {
            ESP_LOGD(LOG_TAG, "setting_press %D %D %D %D [ %S ]\n", i, setting_press[i].layer, setting_press[i].key_num, setting_press[i].action_type, setting_press[i].data);
        } else if (setting_press[i].action_type == 5) {
            memcpy(&mouse_move_input, setting_press[i].data, sizeof(setting_mouse_move));
            ESP_LOGD(LOG_TAG, "setting_press %D %D %D %D [ %D, %D, %D ]\n", i, setting_press[i].layer, setting_press[i].key_num, setting_press[i].action_type, mouse_move_input.x, mouse_move_input.y, mouse_move_input.speed);
        } else {
            ESP_LOGD(LOG_TAG, "setting_press %D %D %D %D\n", i, setting_press[i].layer, setting_press[i].key_num, setting_press[i].action_type);
        }
    }
    ESP_LOGD(LOG_TAG, "mmm: %D %D\n", heap_caps_get_free_size(MALLOC_CAP_32BIT), heap_caps_get_free_size(MALLOC_CAP_8BIT) );

    // Remapに送る用のデータ作成
    int buf_length = layer_max * key_max * 2;
    // Serial.printf("layer_max: %d    key_max: %d    buf_length: %d\n", layer_max, key_max, buf_length);
    setting_remap = new uint8_t[buf_length];
    // バッファ初期化
    for (i=0; i<buf_length; i++) {
        setting_remap[i] = 0x00;
    }
    // キーデータを格納
    for (i=0; i<setting_length; i++) {
        at = setting_press[i].action_type;
        m = (setting_press[i].layer * key_max * 2) + (setting_press[i].key_num * 2);
        if (at == 1) {
            // 通常キー
            memcpy(&normal_input, setting_press[i].data, sizeof(setting_normal_input));
            if (normal_input.key_length < 1) continue;
            s = normal_input.key[0];
            if (normal_input.hold) {
                // holdが定義されていたら tap/hold
                s = normal_input.hold << 8; // 上位8ビットはholdのキー
                if (normal_input.key_length) s |= normal_input.key[0] & 0xFF; // 下位8ビットはタップのキー
            } else if (s >= 0xE0 && s <= 0xE7 && normal_input.key_length > 1) {
                // 1キー目がモデファイアで複数キーが登録してある場合 同時押しと判定
                s = 0;
                for (j=0; j<normal_input.key_length; j++) {
                    k = normal_input.key[j];
                    if (k == 0xE0) { s |= 0x0100; } // 左Ctrl 
                    else if (k == 0xE1) { s |= 0x0200; } // 左Shift
                    else if (k == 0xE2) { s |= 0x0400; } // 左Alt
                    else if (k == 0xE3) { s |= 0x0800; } // 左GUI
                    else if (k == 0xE4) { s |= 0x1100; } // 右Ctrl
                    else if (k == 0xE5) { s |= 0x1200; } // 右Shift
                    else if (k == 0xE6) { s |= 0x1400; } // 右Alt
                    else if (k == 0xE7) { s |= 0x1800; } // 右GUI
                    else { s |= k & 0xFF; } // それ以外は通常キーとして下位8ビットに入れる
                }
            } else {
                // それ以外は通常キー
                if (s == 0x4001) s = 0xF4; // 左クリック
                if (s == 0x4002) s = 0xF5; // 右クリック
                if (s == 0x4004) s = 0xF6; // 中クリック
                if (s == 0x4005) s = 0xFD; // スクロールボタン
            }
            setting_remap[m] = (s >> 8) & 0xff;
            setting_remap[m + 1] = s & 0xff;
        } else if (at == 3) {
            // レイヤー切り替え
            memcpy(&layer_move_input, setting_press[i].data, sizeof(setting_layer_move));
            s = layer_move_input.layer_type; // 切り替えのタイプ
            if (s != 0x50 && s != 0x51 && s != 0x52 && s != 0x53 && s != 0x54 && s != 0x58) s = 0x51; // 不明な指定はMOと判定
            setting_remap[m] = s;
            setting_remap[m + 1] = layer_move_input.layer_id;
        } else if (at == 5) {
            // マウス移動
            memcpy(&mouse_move_input, setting_press[i].data, sizeof(setting_mouse_move));
            s = 0xF0;
            if (mouse_move_input.y < 0) s = 0xF0;
            if (mouse_move_input.y > 0) s = 0xF1;
            if (mouse_move_input.x < 0) s = 0xF2;
            if (mouse_move_input.x > 0) s = 0xF3;
            setting_remap[m] = (s >> 8) & 0xff;
            setting_remap[m + 1] = s & 0xff;
        } else if (at == 6) {
            // 暗記ボタン
            s = 0x3001;
            setting_remap[m] = (s >> 8) & 0xff;
            setting_remap[m + 1] = s & 0xff;
        } else if (at == 7) {
            // LED 設定ボタン
            k = *setting_press[i].data;
            s = 0x00;
            if (k == 0) s = 0x5cbf; // ON / OFF
            if (k == 1) s = 0x5cbe; // 明るさアップ
            if (k == 2) s = 0x5cbd; // 明るさダウン
            if (k == 3) s = 0x5cc0; // 色変更
            if (k == 4) s = 0x5cc1; // 光らせ方変更
            setting_remap[m] = (s >> 8) & 0xff;
            setting_remap[m + 1] = s & 0xff;
        } else if (at == 8) {
            // 打鍵設定ボタン
            k = *setting_press[i].data;
            s = 0x00;
            if (k == 0) s = 0x3010; // サーモグラフ表示
            if (k == 1) s = 0x3011; // 打鍵数をファイルに保存
            if (k == 2) s = 0x3012; // 自動保存設定を変更
            if (k == 3) s = 0x3013; // 打鍵数をファイルに保存
            setting_remap[m] = (s >> 8) & 0xff;
            setting_remap[m + 1] = s & 0xff;
        }
    }
    /* REMAP用バッファデバッグ表示
    Serial.printf("remap_buf (%d):", buf_length);
    for (i=0; i<buf_length; i++) {
        Serial.printf(" %02x", setting_remap[i]);
    }
    Serial.printf("\n");
    */
}

// REMAPで受け取ったデータをJSONデータに書き込む
void AzCommon::remap_save_setting_json() {
    // セッティングJSONを保持する領域
    SpiRamJsonDocument setting_doc(SETTING_JSON_BUF_SIZE);
    JsonObject setting_obj;
    int i, j, k, m, h, l, s;
    JsonObject layer_obj;
    JsonObject keys_obj;
    JsonObject key_obj;
    JsonObject press_obj;
    JsonObject move_obj;
    JsonArray keyarray_obj;
    char lname[32];
    char kname[32];

    // ファイルオープン
    File open_file = SPIFFS.open(SETTING_JSON_PATH);
    if(!open_file) return;
    // 読み込み＆パース
    DeserializationError err = deserializeJson(setting_doc, open_file);
    if (err) return;
    open_file.close();

    // JSONオブジェクトを保持
    setting_obj = setting_doc.as<JsonObject>();

    // 入力モードは無変換の日本語キーボード固定
    setting_obj["keyboard_language"] = 0;
    keyboard_language = 0;

    // キーマップ情報の配列を作成
    setting_obj["layers"].clear();
    for (i=0; i<layer_max; i++) {
        sprintf(lname, "layer_%d", i);
        layer_obj = setting_obj["layers"].createNestedObject(lname);
        layer_obj["name"].set(lname);
        keys_obj = setting_obj["layers"][lname].createNestedObject("keys");
        for (j=0; j<key_max; j++) {
            m = (i * key_max * 2) + (j * 2);
            h = setting_remap[m];
            l = setting_remap[m + 1];
            k = (h << 8) | l;
            if (k == 0) continue;
            // Serial.printf("key: layer=%d key=%d mem=%d id=%d\n", i, j, m, k);
            sprintf(kname, "key_%d", j);
            key_obj = setting_obj["layers"][lname]["keys"].createNestedObject(kname);
            press_obj = setting_obj["layers"][lname]["keys"][kname].createNestedObject("press");
            press_obj["action_type"] = 0;
            if (k <= 0x00E7) {
                // 通常キー
                press_obj["action_type"] = 1; // 通常キー
                press_obj["repeat_interval"] = 51; // 連打無し
                keyarray_obj = setting_obj["layers"][lname]["keys"][kname]["press"].createNestedArray("key");
                keyarray_obj.add(k);
            } else if ((h >= 0x01 && h <= 0x0F) || (h >= 0x11 && h <= 0x1F)) { // 左モデファイア || 右モデファイア
                // モデファイア 同時押し
                press_obj["action_type"] = 1; // 通常キー
                press_obj["repeat_interval"] = 51; // 連打無し
                keyarray_obj = setting_obj["layers"][lname]["keys"][kname]["press"].createNestedArray("key");
                if ((h >> 4) == 0x00) { // 左モデファイア
                    if (h & 0x01) keyarray_obj.add(0xE0); // 左Ctrl
                    if (h & 0x02) keyarray_obj.add(0xE1); // 左Shift
                    if (h & 0x04) keyarray_obj.add(0xE2); // 左Alt
                    if (h & 0x08) keyarray_obj.add(0xE3); // 左GUI
                } else if ((h >> 4) == 0x01) { // 右モデファイア
                    if (h & 0x01) keyarray_obj.add(0xE4); // 右Ctrl
                    if (h & 0x02) keyarray_obj.add(0xE5); // 右Shift
                    if (h & 0x04) keyarray_obj.add(0xE6); // 右Alt
                    if (h & 0x08) keyarray_obj.add(0xE7); // 右GUI
                }
                keyarray_obj.add(l); // 下位8ビットを通常キー
            } else if ((h >= 0x61 && h <= 0x6F) || (h >= 0x71 && h <= 0x7F) || (h >= 0x41 && h <= 0x4F) || h == 0x56) { // 左モデファイア || 右モデファイア || レイヤー || swap?
                // Tap / Hold
                press_obj["action_type"] = 1; // 通常キー
                press_obj["repeat_interval"] = 51; // 連打無し
                press_obj["hold"] = h; // モデファイア | レイヤー定義
                keyarray_obj = setting_obj["layers"][lname]["keys"][kname]["press"].createNestedArray("key");
                keyarray_obj.add(l); // 下位8ビットを通常キー
            } else if ((h == 0x50 || h == 0x51 || h == 0x52 || h == 0x53 || h == 0x54 || h == 0x58) && l < layer_max) {
                // レイヤー切り替え
                press_obj["action_type"] = 3; // レイヤー切り替え
                press_obj["layer"] = l; // 切り替え先レイヤー
                press_obj["layer_type"] = h; // 切り替えの種類
            } else if (k == 0xF0 || k == 0xF1 || k == 0xF2 || k == 0xF3) { // マウス移動↑↓←→
                press_obj["action_type"] = 5; // マウス移動
                move_obj = setting_obj["layers"][lname]["keys"][kname]["press"].createNestedObject("move");
                if (k == 0xF0) { move_obj["x"] = 0; move_obj["y"] = -3; } // 上
                if (k == 0xF1) { move_obj["x"] = 0; move_obj["y"] = 3; } // 下
                if (k == 0xF2) { move_obj["x"] = -3; move_obj["y"] = 0; } // 左
                if (k == 0xF3) { move_obj["x"] = 3; move_obj["y"] = 0; } // 右
                move_obj["speed"] = 100; // 移動速度
            } else if (k == 0xF4 || k == 0xF5 || k == 0xF6 || k == 0xFD) { // マウス ボタン1(左クリック)
                press_obj["action_type"] = 1; // 通常キー
                press_obj["repeat_interval"] = 51; // 連打無し
                keyarray_obj = setting_obj["layers"][lname]["keys"][kname]["press"].createNestedArray("key");
                if (k == 0xF4) s = 0x4001; // 左クリック
                if (k == 0xF5) s = 0x4002; // 右クリック
                if (k == 0xF6) s = 0x4004; // 中クリック
                if (k == 0xFD) s = 0x4005; // スクロールボタン
                keyarray_obj.add(s);
            } else if (h == 0x30 && l == 0x01) { // 暗記ボタン
                press_obj["action_type"] = 6; // 暗記ボタン
            } else if (h == 0x5C && (l == 0xBD || l == 0xBE || l == 0xBF || l == 0xC0 || l == 0xC1)) { // LED設定ボタン
                press_obj["action_type"] = 7; // LED設定ボタン
                if (l == 0xBD) press_obj["led_setting_type"] = 2; // 明るさ ダウン
                if (l == 0xBE) press_obj["led_setting_type"] = 1; // 明るさ アップ
                if (l == 0xBF) press_obj["led_setting_type"] = 0; // ON / OFF
                if (l == 0xC0) press_obj["led_setting_type"] = 3; // カラー変更
                if (l == 0xC1) press_obj["led_setting_type"] = 4; // 光り方変更
            } else if (h == 0x30 && l >= 0x10 && l <= 0x13) { // 打鍵設定ボタン
                press_obj["action_type"] = 8; // 打鍵設定ボタン
                if (l == 0x10) press_obj["dakagi_settype"] = 0; // サーモグラフ表示
                if (l == 0x11) press_obj["dakagi_settype"] = 1; // 打鍵数をファイルに保存
                if (l == 0x12) press_obj["dakagi_settype"] = 2; // 自動保存設定を変更
                if (l == 0x13) press_obj["dakagi_settype"] = 3; // 打鍵数をファイルに保存
            }
        }
    }

    // 変更した内容をファイルに保存
    File save_file = SPIFFS.open(SETTING_JSON_PATH, "w");
    if(!save_file) return;
    serializeJson(setting_doc, save_file);
    save_file.close();

    // メモリ上にあるキーマップを解放
    this->clear_keymap();

    // 新しいキーマップをメモリ上に入れる
    this->get_keymap(setting_obj);
}

// デフォルトレイヤー番号設定
void AzCommon::set_default_layer_no() {
    // キー4が押されていた時 デフォルトを1へ
    if (common_cls.input_key[4] && layers_exists(1)) default_layer_no = 1;
    // キー5が押されていた時 デフォルトを2へ
    if (common_cls.input_key[5] && layers_exists(2)) default_layer_no = 2;
    // キー6が押されていた時 デフォルトを3へ
    if (common_cls.input_key[6] && layers_exists(3)) default_layer_no = 3;
    // キー7が押されていた時 デフォルトを4へ
    if (common_cls.input_key[7] && layers_exists(4)) default_layer_no = 4;
    // 今選択してるレイヤーをデフォルトに
    select_layer_no = default_layer_no;
}

// キーボードタイプの番号を取得する
void AzCommon::get_keyboard_type_int(String t) {
    if (t.equals("az_macro")) {
        keyboard_type_int = 1;
    } else if (t.equals("az_66jp")) {
        keyboard_type_int = 2;
    } else if (t.equals("az_4key")) {
        keyboard_type_int = 3;
    }
}

// ユニットのタイプ番号を取得する
void AzCommon::get_option_type_int(JsonObject setting_obj) {
    String t = setting_obj["option_set"]["type"].as<String>();
    option_type_int = 0;
    if (t.equals("foot_m")) {
        // 踏みキー
        option_type_int = 1;
        if (setting_obj["option_set"]["inversion"].as<signed int>()) {
            foot_inversion = true;
        } else {
            foot_inversion = false;
        }
        
    } else if (t.equals("trackball_m")) {
        // トラックボール
        option_type_int = 2;
        // トラックボールの向きもここで取得
        if (setting_obj["option_set"].containsKey("trackball_direction")) {
            trackball_direction = setting_obj["option_set"]["trackball_direction"].as<signed int>();
        } else {
            trackball_direction = 0;
        }
        // トラックボールの速度も取得
        if (setting_obj["option_set"].containsKey("trackball_speed")) {
            trackball_speed = setting_obj["option_set"]["trackball_speed"].as<signed int>();
        } else {
            trackball_speed = 10;
        }
    } else if (t.equals("display_m")) {
        // AZ-Macro用 液晶モジュール
        option_type_int = 3;
    } else if (t.equals("display_66jp")) {
        // AZ-66JP用 液晶モジュール
        option_type_int = 4;
    }
}


// ファイルを開いてテキストをロードする
int AzCommon::read_file(char *file_path, String &read_data) {
    ESP_LOGD(LOG_TAG, "read file: %S\n", file_path);
    // ファイルが無ければエラー
    if (!SPIFFS.exists(file_path)) {
        ESP_LOGD(LOG_TAG, "read_file not file: %S\n", file_path);
        return 0;
    }
    // ファイルオープン
    File fp = SPIFFS.open(file_path, "r");
    if(!fp){
        ESP_LOGD(LOG_TAG, "read_file open error: %S\n", file_path);
        return 0;
    }
    // 読み込み
    read_data = fp.readString();
    fp.close();
    return 1;
}

// テキストをファイルに書き込む
int AzCommon::write_file(char *file_path, String &write_data) {
    // 書込みモードでファイルオープン
      ESP_LOGD(LOG_TAG, "write_file open path: %S\n", file_path);
    File fp = SPIFFS.open(file_path, FILE_WRITE);
    if(!fp){
        ESP_LOGD(LOG_TAG, "write_file open error: %S\n", file_path);
        return 0;
    }
    // 書込み
    ESP_LOGD(LOG_TAG, "save");
    if(!fp.print(write_data)){
        ESP_LOGD(LOG_TAG, "write_file print error");
        fp.close();
        return 0;
    }
    fp.close();
    ESP_LOGD(LOG_TAG, "write_file print ok");
    return 1;
}

// ファイルを削除
int AzCommon::remove_file(char *file_path) {
    if (SPIFFS.remove(file_path)) {
        return 1;
    } else {
        return 0;
    }
}


// デフォルトのsetting.jsonを生成する
bool AzCommon::create_setting_json() {
    // 書込みモードでファイルオープン
    File json_file = SPIFFS.open(SETTING_JSON_PATH, FILE_WRITE);
    if(!json_file){
        ESP_LOGD(LOG_TAG, "create_setting_json open error");
        return false;
    }
    // 書込み
    if(!json_file.print(setting_default_json_bin)){
        ESP_LOGD(LOG_TAG, "create_setting_json print error");
        json_file.close();
        return false;
    }
    json_file.close();
    ESP_LOGD(LOG_TAG, "create_setting_json print ok");
    return true;
}

// キーの入力ピンの初期化
void AzCommon::pin_setup() {
    // output ピン設定 (colで定義されているピンを全てoutputにする)
    int i;
    for (i=0; i<col_len; i++) {
        if (!AZ_DEBUG_MODE || (col_list[i] != 1 && col_list[i] != 3)) pinMode(col_list[i], OUTPUT_OPEN_DRAIN);
    }
    // row で定義されているピンを全てinputにする
    for (i=0; i<row_len; i++) {
        if (!AZ_DEBUG_MODE || (row_list[i] != 1 && row_list[i] != 3)) pinMode(row_list[i], INPUT_PULLUP);
    }
    // direct(スイッチ直接続)で定義されているピンを全てinputにする
    for (i=0; i<direct_len; i++) {
        pinMode(direct_list[i], INPUT_PULLUP);
    }
    // キー数の計算
    key_input_length = (col_len * row_len) + direct_len + touch_len;
    if (key_input_length > KEY_INPUT_MAX) key_input_length = KEY_INPUT_MAX;
    ESP_LOGD(LOG_TAG, "key length : %D\r\n", key_input_length);
    // キー入力ピン初期化のキーボード別の処理
    pin_setup_sub_process();
    // 打鍵数リセット
    for (i=0; i<KEY_INPUT_MAX; i++) {
        this->key_count[i] = 0;
    }
    this->key_count_total = 0;
}


// キー入力ピン初期化のキーボード別の処理
void AzCommon::pin_setup_sub_process() {
    if (option_type_int == 1) {
        // 踏みキー
        pinMode(27, INPUT_PULLUP);
    }
}

// レイヤーが存在するか確認
bool AzCommon::layers_exists(int layer_no) {
    int i;
    for (i=0; i<setting_length; i++) {
        if (setting_press[i].layer == layer_no) return true;
    }
    return false;
}

// 指定したキーの入力設定オブジェクトを取得する
setting_key_press AzCommon::get_key_setting(int layer_id, int key_num) {
    int i;
    for (i=0; i<setting_length; i++) {
        if (setting_press[i].layer == layer_id && setting_press[i].key_num == key_num) return setting_press[i];
    }
    setting_key_press r;
    r.layer = -1;
    r.key_num = -1;
    r.action_type = -1;
    return r;
}


//データをEEPROMから読み込む。保存データが無い場合デフォルトにする。
void AzCommon::load_data() {
    // EEPROM初期化
    EEPROM.begin(EEPROM_BUF_SIZE);
    ESP_LOGD(LOG_TAG, "eeprom size: %D", EEPROM.length());
    ESP_LOGD(LOG_TAG, "eeprom load\r\n");
    EEPROM.get<mrom_data_set>(0, eep_data);
    ESP_LOGD(LOG_TAG, "eeprom check: %S", eep_data.check);
    if (strcmp(eep_data.check, EEP_DATA_VERSION)) { //バージョンをチェック
        ESP_LOGD(LOG_TAG, "eeprom set default\r\n");
        //保存データが無い場合デフォルトを設定
        // 起動モード
        eep_data.boot_mode = 0;
        // データチェック文字列
        strcpy(eep_data.check, EEP_DATA_VERSION);
        // WIFIアクセスポイントの名前
        char b[16];
        getRandomNumbers(4, b);
        sprintf(eep_data.ap_ssid, "%S-%S", WIFI_AP_SSI_NAME, b);
        // ユニークID
        getRandomNumbers(10, eep_data.uid);
        // 受け渡し用テキスト
        strcpy(eep_data.text, "");
        // 設定JSONも作り直す
        create_setting_json();
        // キーボードモードで再起動(ここでeep_dataも保存される)
        change_mode(0);
    }
}


// データをEEPROMに書き込む
void AzCommon::save_data() {
    //EEPROMに設定を保存する。
    strcpy(eep_data.check, EEP_DATA_VERSION);
    ESP_LOGD(LOG_TAG, "save eeprom boot mode: %D", eep_data.boot_mode);
    ESP_LOGD(LOG_TAG, "save eeprom check sum: %S", eep_data.check);
    ESP_LOGD(LOG_TAG, "text: %S", eep_data.text);
    ESP_LOGD(LOG_TAG, "data sizeof: %D", sizeof(mrom_data_set));
    EEPROM.put<mrom_data_set>(0, eep_data);
    delay(200);
    EEPROM.commit(); //大事
    delay(200);
    ESP_LOGD(LOG_TAG, "save complete\r\n");
}

// 起動回数読み込み
void AzCommon::load_boot_count() {
    File fp;
    boot_count = 0;
    // ファイルが無い場合はデフォルトファイル作成
    if (SPIFFS.exists(BOOT_COUNT_PATH)) {
        // boot_count から読み込み
        fp = SPIFFS.open(BOOT_COUNT_PATH, "r");
        if(!fp){
            ESP_LOGD(LOG_TAG, "boot count file open error\n");
            return;
        }
        if (fp.available()) {
            fp.read((uint8_t *)&boot_count, 4);
        }
        fp.close();
    }
    // カウントアップ
    boot_count++;
    // ファイルに書き込み
    fp = SPIFFS.open(BOOT_COUNT_PATH, "w");
    fp.write((uint8_t *)&boot_count, 4);
    fp.close();
}


// ファイルから設定値を読み込み
void AzCommon::load_file_data(char *file_path, uint8_t *load_point, uint16_t load_size) {
    File fp;
    // ファイルが無い場合は何もしない
    if (!SPIFFS.exists(file_path)) return;
    // ファイル読み込み
    fp = SPIFFS.open(file_path, "r");
    if(!fp){
        ESP_LOGD(LOG_TAG, "file open error\n");
        return;
    }
    if (fp.available()) {
        fp.read(load_point, load_size);
    }
    fp.close();
}


// ファイルに設定値を書込み
void AzCommon::save_file_data(char *file_path, uint8_t *save_point, uint16_t save_size) {
    // ファイルに書き込み
    File fp;
    fp = SPIFFS.open(file_path, "w");
    fp.write(save_point, save_size);
    fp.close();
}


// 起動モードを変更してEEPROMに保存
void AzCommon::set_boot_mode(int set_mode) {
    eep_data.boot_mode = set_mode;
    save_data();
}

// モードを切り替えて再起動
void AzCommon::change_mode(int set_mode) {
    set_boot_mode(set_mode);
    ESP.restart(); // ESP32再起動
}


// 現在のキーの入力状態を取得
void AzCommon::key_read(void) {
    int i, j, n, s;
    n = 0;
    // ダイレクト入力の取得
    for (i=0; i<direct_len; i++) {
        input_key[n] = !digitalRead(direct_list[i]);
        n++;
    }
    // タッチ入力の取得
    for (i=0; i<touch_len; i++) {
        if (touchRead(touch_list[i]) < 25) {
            input_key[n] = 1;
        } else {
            input_key[n] = 0;
        }
        n++;
    }
    // マトリックス入力の取得
    for (i=0; i<col_len; i++) {
        // 対象のcolピンのみ lowにする
        for (j=0; j<col_len; j++) {
            if (i == j) { s = 0; } else { s = 1; }
            if (!AZ_DEBUG_MODE || (col_list[j] != 1 && col_list[j] != 3)) digitalWrite(col_list[j], s);
        }
        delayMicroseconds(50);
        // row の分キー入力チェック
        for (j=0; j<row_len; j++) {
            input_key[n] = !digitalRead(row_list[j]);
            n++;
        }
    }
    // キーボード別の後処理
    key_read_sub_process();
}

// キーボード別の後処理
void AzCommon::key_read_sub_process(void) {
    if (option_type_int == 1) {
        // 踏みキー
        if (foot_inversion && digitalRead(27) == 0) {
            // ジャックが刺されている間はON/OFF を反転
            input_key[8] = ! input_key[8];
            input_key[9] = ! input_key[9];
        }
    }
}

// 今回の入力状態を保持
void AzCommon::key_old_copy(void) {
    int i;
    for (i=0; i<key_input_length; i++) {
        input_key_last[i] = input_key[i];
    }
}

// 液晶ユニットが付いているか
bool AzCommon::on_tft_unit(void) {
    if (option_type_int == 3 || option_type_int == 4) {
        return true;
    }
    return false;
}

// 全てのファイルを削除
void AzCommon::delete_all(void) {
    File dirp = SPIFFS.open("/");
    File filep = dirp.openNextFile();
    while(filep){
        SPIFFS.remove(filep.name());
        filep = dirp.openNextFile();
    }
}

// 指定した文字から始まるファイルすべて削除
void AzCommon::delete_indexof_all(String check_str) {
    File dirp = SPIFFS.open("/");
    File filep = dirp.openNextFile();
    String file_path;
    while(filep){
        file_path = String(filep.name());
        if (file_path.indexOf("/" + check_str) == 0) {
            SPIFFS.remove(file_path);
        }
        filep = dirp.openNextFile();
    }
}

// ファイル領域合計サイズを取得
int AzCommon::spiffs_total(void) {
    return SPIFFS.totalBytes();
}

// 使用しているファイル領域サイズを取得
int AzCommon::spiffs_used(void) {
    return SPIFFS.usedBytes();
}
