palette-system/az-macro/firmware/az_keyboard/src/keyboard/setting_azmacro_default.h

// file name : setting_azmacro_default.json
// file size : 1688 bytes

const char setting_default_json_bin[] PROGMEM = {
  0x7b,0x0d,0x0a,0x09,0x22,0x61,0x70,0x22,0x3a,0x20,0x7b,0x0d,0x0a,0x09,0x09,0x22,
  0x70,0x61,0x73,0x73,0x22,0x3a,0x20,0x22,0x22,0x0d,0x0a,0x09,0x7d,0x2c,0x0d,0x0a,
  0x09,0x22,0x77,0x69,0x66,0x69,0x22,0x3a,0x20,0x5b,0x5d,0x2c,0x0d,0x0a,0x09,0x22,
  0x76,0x65,0x6e,0x64,0x6f,0x72,0x49,0x64,0x22,0x3a,0x20,0x22,0x30,0x78,0x65,0x35,
  0x30,0x32,0x22,0x2c,0x0d,0x0a,0x09,0x22,0x70,0x72,0x6f,0x64,0x75,0x63,0x74,0x49,
  0x64,0x22,0x3a,0x20,0x22,0x30,0x78,0x30,0x32,0x30,0x30,0x22,0x2c,0x0d,0x0a,0x09,
  0x22,0x73,0x74,0x61,0x74,0x75,0x73,0x5f,0x70,0x69,0x6e,0x22,0x3a,0x20,0x33,0x32,
  0x2c,0x0d,0x0a,0x09,0x22,0x72,0x67,0x62,0x5f,0x70,0x69,0x6e,0x22,0x3a,0x20,0x2d,
  0x31,0x2c,0x0d,0x0a,0x09,0x22,0x72,0x67,0x62,0x5f,0x6c,0x65,0x6e,0x22,0x3a,0x20,
  0x30,0x2c,0x0d,0x0a,0x09,0x22,0x6d,0x61,0x74,0x72,0x69,0x78,0x5f,0x72,0x6f,0x77,
  0x22,0x3a,0x20,0x30,0x2c,0x0d,0x0a,0x09,0x22,0x6d,0x61,0x74,0x72,0x69,0x78,0x5f,
  0x63,0x6f,0x6c,0x22,0x3a,0x20,0x30,0x2c,0x0d,0x0a,0x09,0x22,0x6c,0x65,0x64,0x5f,
  0x6e,0x75,0x6d,0x22,0x3a,0x20,0x5b,0x5d,0x2c,0x0d,0x0a,0x09,0x22,0x6b,0x65,0x79,
  0x5f,0x6d,0x61,0x74,0x72,0x69,0x78,0x22,0x3a,0x20,0x5b,0x5d,0x2c,0x0d,0x0a,0x09,
  0x22,0x6b,0x65,0x79,0x62,0x6f,0x61,0x72,0x64,0x5f,0x6c,0x61,0x6e,0x67,0x75,0x61,
  0x67,0x65,0x22,0x3a,0x20,0x30,0x2c,0x0d,0x0a,0x09,0x22,0x6b,0x65,0x79,0x62,0x6f,
  0x61,0x72,0x64,0x5f,0x74,0x79,0x70,0x65,0x22,0x3a,0x20,0x22,0x61,0x7a,0x5f,0x6d,
  0x61,0x63,0x72,0x6f,0x22,0x2c,0x0d,0x0a,0x09,0x22,0x6b,0x65,0x79,0x62,0x6f,0x61,
  0x72,0x64,0x5f,0x70,0x69,0x6e,0x22,0x3a,0x20,0x7b,0x0d,0x0a,0x09,0x09,0x22,0x72,
  0x6f,0x77,0x22,0x3a,0x20,0x5b,0x5d,0x2c,0x0d,0x0a,0x09,0x09,0x22,0x63,0x6f,0x6c,
  0x22,0x3a,0x20,0x5b,0x5d,0x2c,0x0d,0x0a,0x09,0x09,0x22,0x64,0x69,0x72,0x65,0x63,
  0x74,0x22,0x3a,0x20,0x5b,0x32,0x33,0x2c,0x20,0x32,0x32,0x2c,0x20,0x32,0x31,0x2c,
  0x20,0x31,0x39,0x2c,0x20,0x31,0x36,0x2c,0x20,0x31,0x37,0x2c,0x20,0x35,0x2c,0x20,
  0x31,0x38,0x5d,0x2c,0x0d,0x0a,0x09,0x09,0x22,0x74,0x6f,0x75,0x63,0x68,0x22,0x3a,
  0x20,0x5b,0x5d,0x0d,0x0a,0x09,0x7d,0x2c,0x0d,0x0a,0x09,0x22,0x64,0x65,0x66,0x61,
  0x75,0x6c,0x74,0x5f,0x6c,0x61,0x79,0x65,0x72,0x22,0x3a,0x20,0x30,0x2c,0x0d,0x0a,
  0x09,0x22,0x6c,0x61,0x79,0x65,0x72,0x73,0x22,0x3a,0x20,0x7b,0x0d,0x0a,0x09,0x09,
  0x22,0x6c,0x61,0x79,0x65,0x72,0x5f,0x30,0x22,0x3a,0x20,0x7b,0x0d,0x0a,0x09,0x09,
  0x09,0x22,0x6e,0x61,0x6d,0x65,0x22,0x3a,0x20,0x22,0xe3,0x83,0xac,0xe3,0x82,0xa4,
  0xe3,0x83,0xa4,0xe3,0x83,0xbc,0x30,0x22,0x2c,0x0d,0x0a,0x09,0x09,0x09,0x22,0x6b,
  0x65,0x79,0x73,0x22,0x3a,0x20,0x7b,0x0d,0x0a,0x09,0x09,0x09,0x09,0x22,0x6b,0x65,
  0x79,0x5f,0x30,0x22,0x3a,0x20,0x7b,0x0d,0x0a,0x09,0x09,0x09,0x09,0x09,0x22,0x70,
  0x72,0x65,0x73,0x73,0x22,0x3a,0x20,0x7b,0x0d,0x0a,0x09,0x09,0x09,0x09,0x09,0x09,
  0x22,0x61,0x63,0x74,0x69,0x6f,0x6e,0x5f,0x74,0x79,0x70,0x65,0x22,0x3a,0x20,0x31,
  0x2c,0x0d,0x0a,0x09,0x09,0x09,0x09,0x09,0x09,0x22,0x6b,0x65,0x79,0x22,0x3a,0x20,
  0x5b,0x34,0x5d,0x0d,0x0a,0x09,0x09,0x09,0x09,0x09,0x7d,0x2c,0x0d,0x0a,0x09,0x09,
  0x09,0x09,0x09,0x22,0x6c,0x6f,0x6e,0x67,0x5f,0x70,0x72,0x65,0x73,0x73,0x22,0x3a,
  0x20,0x7b,0x7d,0x2c,0x0d,0x0a,0x09,0x09,0x09,0x09,0x09,0x22,0x6c,0x6f,0x6e,0x67,
  0x5f,0x70,0x72,0x65,0x73,0x73,0x5f,0x74,0x69,0x6d,0x65,0x22,0x3a,0x20,0x30,0x0d,
  0x0a,0x09,0x09,0x09,0x09,0x7d,0x2c,0x0d,0x0a,0x09,0x09,0x09,0x09,0x22,0x6b,0x65,
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
};
