palette-system/az-macro/firmware/writer/az66jp_writer/index_bin.h

// file name : writer.html
// file size : 5119 bytes

const char index_bin[] PROGMEM = {
  0x3c,0x21,0x44,0x4f,0x43,0x54,0x59,0x50,0x45,0x20,0x68,0x74,0x6d,0x6c,0x3e,0x0d,
  0x0a,0x3c,0x68,0x74,0x6d,0x6c,0x3e,0x0d,0x0a,0x3c,0x68,0x65,0x61,0x64,0x3e,0x0d,
  0x0a,0x20,0x20,0x3c,0x6d,0x65,0x74,0x61,0x20,0x63,0x68,0x61,0x72,0x73,0x65,0x74,
  0x3d,0x22,0x55,0x54,0x46,0x2d,0x38,0x22,0x20,0x2f,0x3e,0x0d,0x0a,0x20,0x20,0x3c,
  0x6d,0x65,0x74,0x61,0x20,0x6e,0x61,0x6d,0x65,0x3d,0x22,0x76,0x69,0x65,0x77,0x70,
  0x6f,0x72,0x74,0x22,0x20,0x63,0x6f,0x6e,0x74,0x65,0x6e,0x74,0x3d,0x22,0x77,0x69,
  0x64,0x74,0x68,0x3d,0x33,0x30,0x30,0x2c,0x20,0x69,0x6e,0x69,0x74,0x69,0x61,0x6c,
  0x2d,0x73,0x63,0x61,0x6c,0x65,0x3d,0x30,0x2e,0x35,0x35,0x2c,0x20,0x6d,0x61,0x78,
  0x69,0x6d,0x75,0x6d,0x2d,0x73,0x63,0x61,0x6c,0x65,0x3d,0x30,0x2e,0x35,0x35,0x2c,
  0x20,0x75,0x73,0x65,0x72,0x2d,0x73,0x63,0x61,0x6c,0x61,0x62,0x6c,0x65,0x3d,0x6e,
  0x6f,0x22,0x3e,0x0d,0x0a,0x20,0x20,0x3c,0x74,0x69,0x74,0x6c,0x65,0x3e,0x66,0x69,
  0x72,0x6d,0x77,0x61,0x72,0x65,0x20,0x77,0x72,0x69,0x74,0x65,0x72,0x3c,0x2f,0x74,
  0x69,0x74,0x6c,0x65,0x3e,0x0d,0x0a,0x20,0x20,0x3c,0x73,0x74,0x79,0x6c,0x65,0x3e,
  0x3c,0x21,0x2d,0x2d,0x0d,0x0a,0x68,0x74,0x6d,0x6c,0x20,0x7b,0x0d,0x0a,0x20,0x20,
  0x2d,0x6d,0x73,0x2d,0x75,0x73,0x65,0x72,0x2d,0x73,0x65,0x6c,0x65,0x63,0x74,0x3a,
  0x20,0x6e,0x6f,0x6e,0x65,0x3b,0x0d,0x0a,0x20,0x20,0x2d,0x6d,0x6f,0x7a,0x2d,0x75,
  0x73,0x65,0x72,0x2d,0x73,0x65,0x6c,0x65,0x63,0x74,0x3a,0x20,0x2d,0x6d,0x6f,0x7a,
  0x2d,0x6e,0x6f,0x6e,0x65,0x3b,0x0d,0x0a,0x20,0x20,0x2d,0x6b,0x68,0x74,0x6d,0x6c,
  0x2d,0x75,0x73,0x65,0x72,0x2d,0x73,0x65,0x6c,0x65,0x63,0x74,0x3a,0x20,0x6e,0x6f,
  0x6e,0x65,0x3b,0x0d,0x0a,0x20,0x20,0x2d,0x77,0x65,0x62,0x6b,0x69,0x74,0x2d,0x75,
  0x73,0x65,0x72,0x2d,0x73,0x65,0x6c,0x65,0x63,0x74,0x3a,0x20,0x6e,0x6f,0x6e,0x65,
  0x3b,0x0d,0x0a,0x20,0x20,0x75,0x73,0x65,0x72,0x2d,0x73,0x65,0x6c,0x65,0x63,0x74,
  0x3a,0x20,0x6e,0x6f,0x6e,0x65,0x3b,0x0d,0x0a,0x20,0x20,0x20,0x20,0x6f,0x75,0x74,
  0x6c,0x69,0x6e,0x65,0x20,0x3a,0x20,0x6e,0x6f,0x6e,0x65,0x3b,0x0d,0x0a,0x7d,0x0d,
  0x0a,0x62,0x6f,0x64,0x79,0x20,0x7b,0x0d,0x0a,0x20,0x20,0x20,0x20,0x6d,0x61,0x72,
  0x67,0x69,0x6e,0x3a,0x20,0x30,0x3b,0x0d,0x0a,0x20,0x20,0x20,0x20,0x70,0x61,0x64,
  0x64,0x69,0x6e,0x67,0x3a,0x20,0x30,0x3b,0x0d,0x0a,0x20,0x20,0x2d,0x6d,0x73,0x2d,
  0x75,0x73,0x65,0x72,0x2d,0x73,0x65,0x6c,0x65,0x63,0x74,0x3a,0x20,0x6e,0x6f,0x6e,
  0x65,0x3b,0x0d,0x0a,0x20,0x20,0x2d,0x6d,0x6f,0x7a,0x2d,0x75,0x73,0x65,0x72,0x2d,
  0x73,0x65,0x6c,0x65,0x63,0x74,0x3a,0x20,0x2d,0x6d,0x6f,0x7a,0x2d,0x6e,0x6f,0x6e,
  0x65,0x3b,0x0d,0x0a,0x20,0x20,0x2d,0x6b,0x68,0x74,0x6d,0x6c,0x2d,0x75,0x73,0x65,
  0x72,0x2d,0x73,0x65,0x6c,0x65,0x63,0x74,0x3a,0x20,0x6e,0x6f,0x6e,0x65,0x3b,0x0d,
  0x0a,0x20,0x20,0x2d,0x77,0x65,0x62,0x6b,0x69,0x74,0x2d,0x75,0x73,0x65,0x72,0x2d,
  0x73,0x65,0x6c,0x65,0x63,0x74,0x3a,0x20,0x6e,0x6f,0x6e,0x65,0x3b,0x0d,0x0a,0x20,
  0x20,0x75,0x73,0x65,0x72,0x2d,0x73,0x65,0x6c,0x65,0x63,0x74,0x3a,0x20,0x6e,0x6f,
  0x6e,0x65,0x3b,0x0d,0x0a,0x20,0x20,0x20,0x20,0x66,0x6f,0x6e,0x74,0x2d,0x73,0x69,
  0x7a,0x65,0x3a,0x20,0x33,0x30,0x3b,0x0d,0x0a,0x20,0x20,0x20,0x20,0x62,0x61,0x63,
  0x6b,0x67,0x72,0x6f,0x75,0x6e,0x64,0x2d,0x63,0x6f,0x6c,0x6f,0x72,0x3a,0x20,0x23,
  0x39,0x30,0x63,0x31,0x66,0x34,0x3b,0x0d,0x0a,0x7d,0x0d,0x0a,0x66,0x6f,0x72,0x6d,
  0x20,0x7b,0x0d,0x0a,0x20,0x20,0x20,0x20,0x6d,0x61,0x72,0x67,0x69,0x6e,0x3a,0x20,
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
};
